LinkItONEDevGroup/LASS/IASS/IASS_BASIC/Docs/IASS完整安裝說明.pdf

1

# 開源的 IASS 室內環控系統

## Every One Can DIY Your Own Sensor Device

### IASS 是一套免費開源的室內環控系統，最早由凌陽創新科技開發並免費釋出。透過

### Arduino 開發板，搭配市面上常見且價廉物美的感測器，不需要撰寫任何程式，希望讓任

### 何人皆能在 30 分鐘內行 DIY 組裝完成符合自己需求的感測裝置。

### IASS 開源程式碼下載：https://github.com/LinkItONEDevGroup/LASS/tree/master/IASS

### IASS 目前為 LASS 的一個子計劃，也歡迎開發者們加入 IASS 予以修改精進，並持續增

### 加新的功能，如果您有興趣，請加入 LASS 的 FB 社團：

### https://www.facebook.com/groups/1607718702812067/

2

3

4

### A) IASS 特色

### 任何人皆能 DIY 感測裝置：

不需要程式設計或相關電子工程知識，每個人皆能 DIY 自己的環控系統。

### 支援多種感測功能：

目前支援 12 種環境感應功能：溫度,溼度,漏水,噪音,一氧化碳,天然氣, PM2.5, PM10, PM100, 二氧

化碳,環境光照度，可依自身需求決定要加裝的感應器。

### 不需要撰寫程式：

提供現成的 Arduino 程式可直接使用，分為 sensor 與 device 兩種，使用者可依需求選擇不同的

sensors 程式搭配成 device。

### 提供預設搭配好的感測裝置：

除了使用者可自行搭配決定感測器種類外，亦提供預設數種 device 直接使用：

- Office 辦公室：溫溼、PM2.5、CO2、光照度
- 電腦機房：溫溼、漏水、可燃氣體
- 家居室內：溫溼、一氧化碳、天然氣

### 自動上傳 ThingSpeak：

您可以讓組裝後的 IASS device 將資料自動上傳 ThingSpeak 以提供遠端瀏覽觀看（需自行註冊

ThingSpeak 帳號並於程式中放入 API KEY）

### 支援上傳指定 server：

除上傳 ThingSpeak 之外，亦可選擇將資料傳送到指定的 server 來接收(使用 GET)，目前 IASS 也

有提供一 PHP 編寫的中控台網站。

### B) IASS 的安裝步驟

5

A.1) 選擇您需要的感測裝置類型，購買零件材料開始 IY。

IASS 目前提供下列三種組裝範例。

- 辦公室專用
- 居家安全專用
- 機房專用

您也可以從 IASS GitHub 的 Sensors_support 目錄中選擇需要的感應器程式來組裝自己的感應裝

置。

A.2) 決定您的裝置要將資料上傳 ThingSpeak 還是傳到特定的伺服器。

- 若要上傳 ThingSpeak，請選擇 _thingspeak 資料夾的 Arduino 程式。
- 若要傳到指定伺服器，請選擇 _selfserver 資料夾的 Arduino 程式。

A.3) 決定是否要加裝 LCD？

A.4) 開始燒錄 Arduino 程式。

A.5) 如果您選擇上傳 ThingSpeak，可開始進行 ThingSpeak 設定

如果您選擇傳到 IASS 的伺服器，請開始安裝設定主機環境。

### C) 辦公室專用感測裝置的安裝步驟

材料準備

本裝置範例支援溫溼、PM2.5、CO2 及光照度等四種感測器功能，所需要的材料如下：

1. | Arduino UNO 主板 | x 1

http://www.icshop.com.tw/product_info.php/products_id/20369

2. | W5100 R3 network shield | x 1

http://goods.ruten.com.tw/item/show?21434006463160

3. | DHT-22 sensor | x 1（溫溼度用）

http://www.icshop.com.tw/product_info.php/products_id/12478

4. | G3 PM2.5 感測器 | x 1（PM2.5 用）

http://www.icshop.com.tw/product_info.php/products_id/20460

6

5. | CO2 感測器 MH-Z16 | x 1（二氧化碳用）

http://www.icshop.com.tw/product_info.php/products_id/14133

6. | 光照度感測器 TEMT6000 | x 1（光照度使用）

http://www.icshop.com.tw/product_info.php/products_id/11432

7. | 9V 變壓器 | x 1

（如果您同時裝上很多感應器，建議使用 9V 變壓器取代 USB，以避免電源不足）

http://www.icshop.com.tw/product_info.php/products_id/17470

8. | 迷你麵包板 | x 1

http://www.icshop.com.tw/product_info.php/products_id/11516

9. | 杜邦線 | 數條

http://www.icshop.com.tw/product_info.php/products_id/12374

10. 小型Ｌ型立書夾 | x 1（$39 元店有很多）

準備好了？開始組裝吧！

溫溼度感測

A）首先，將材料#1 與材料#2 合體如下：

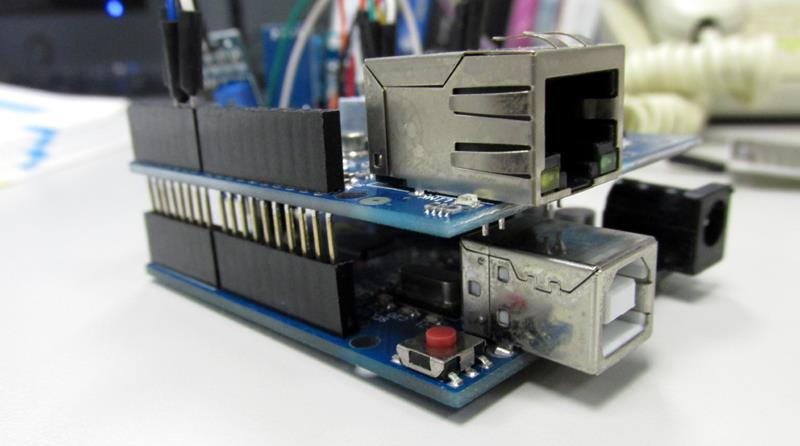
[picture p16: figure]

B）把材料#3 插上，注意一下左圖它的腳位

7

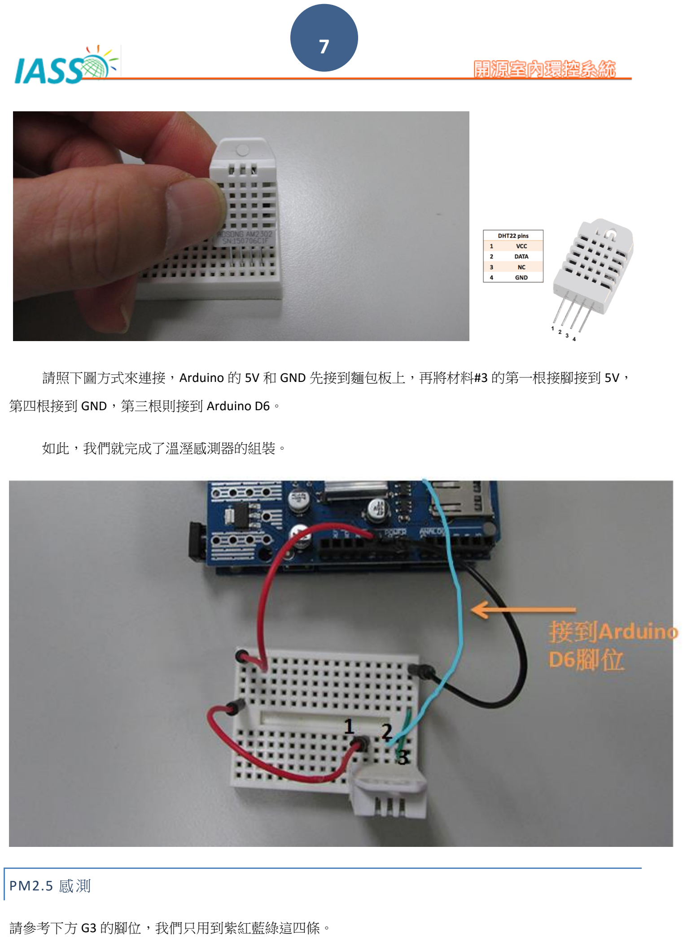
[picture p17: page 7]

請照下圖方式來連接，Arduino 的 5V 和 GND 先接到麵包板上，再將材料#3 的第一根接腳接到 5V，

第四根接到 GND，第三根則接到 Arduino D6。

如此，我們就完成了溫溼感測器的組裝。

PM2.5 感測

請參考下方 G3 的腳位，我們只用到紫紅藍綠這四條。

8

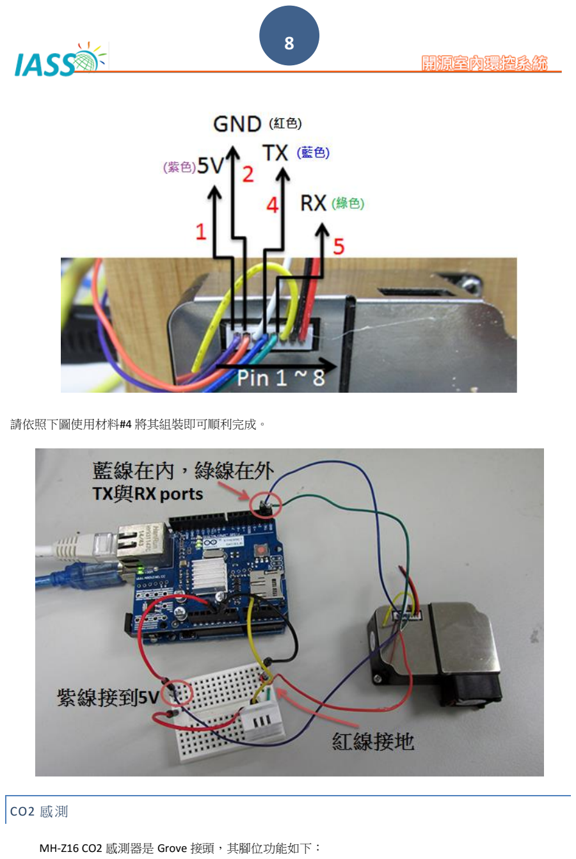
[picture p18: page 8]

請依照下圖使用材料#4 將其組裝即可順利完成。

CO2 感測

MH-Z16 CO2 感測器是 Grove 接頭，其腳位功能如下：

9

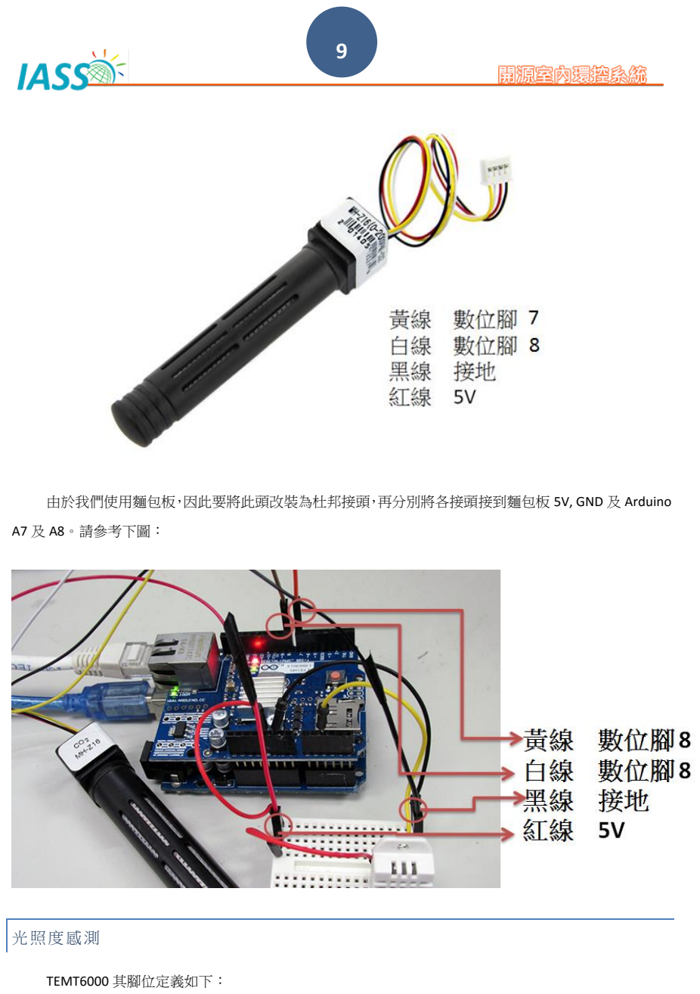
[picture p19: page 9]

由於我們使用麵包板，因此要將此頭改裝為杜邦接頭，再分別將各接頭接到麵包板 5V, GND 及 Arduino

A7 及 A8。請參考下圖：

光照度感測

TEMT6000 其腳位定義如下：

10

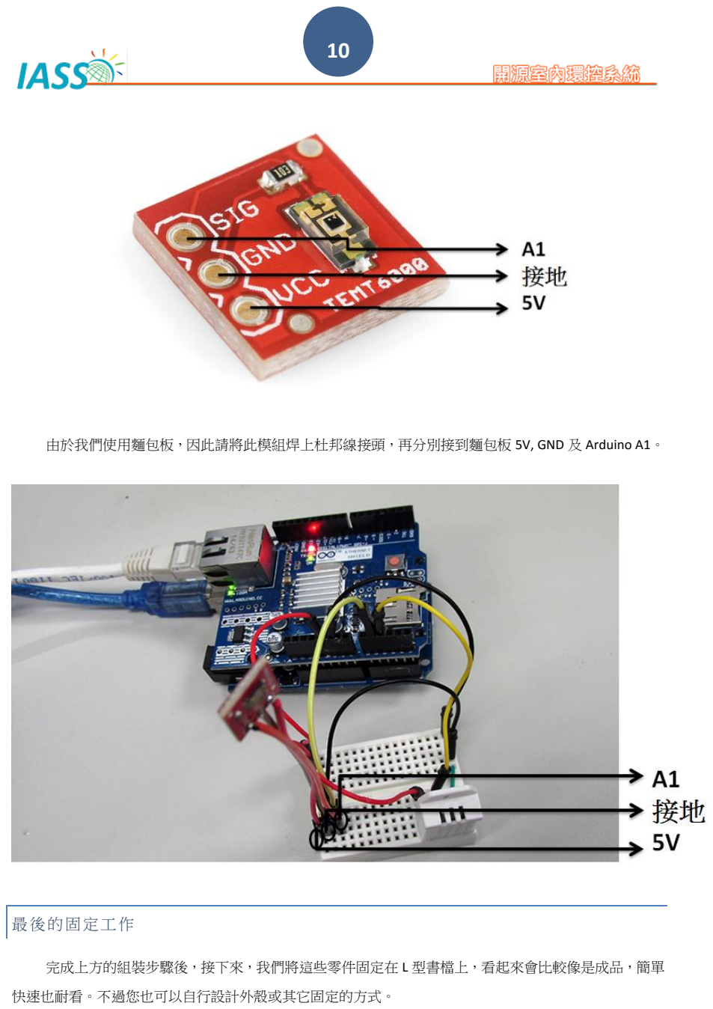
[picture p20: page 10]

由於我們使用麵包板，因此請將此模組焊上杜邦線接頭，再分別接到麵包板 5V, GND 及 Arduino A1。

最後的固定工作

完成上方的組裝步驟後，接下來，我們將這些零件固定在 L 型書檔上，看起來會比較像是成品，簡單

快速也耐看。不過您也可以自行設計外殼或其它固定的方式。

11

L 型書檔如果您使用的是木板材質，那麼可以直接用螺絲釘將所材料零件鎖上固定，如果使用的是鐵

或塑膠材質，那麼可能需要使用熱熔膠來固定。

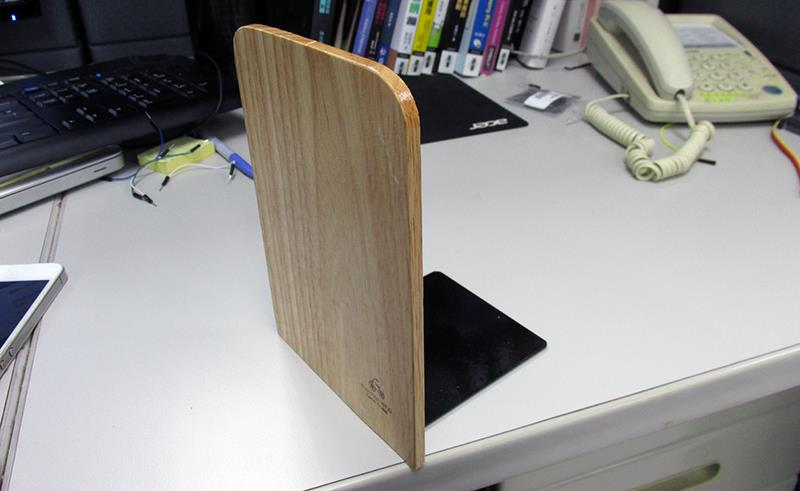
[picture p21: figure]

先將各零件要擺放位置先來預排看看。由於我們做的是一台可偵測溫溼度、PM2.5、二氧化碳、環境

光照度的感測裝置，因此有總共四個零件（Arduino 主板+W5100、迷你麵包板、G3 PM2.5 感測器、CO2 感

測器），把所有零件依照上述方式組裝好之後，預定擺放位置如下：

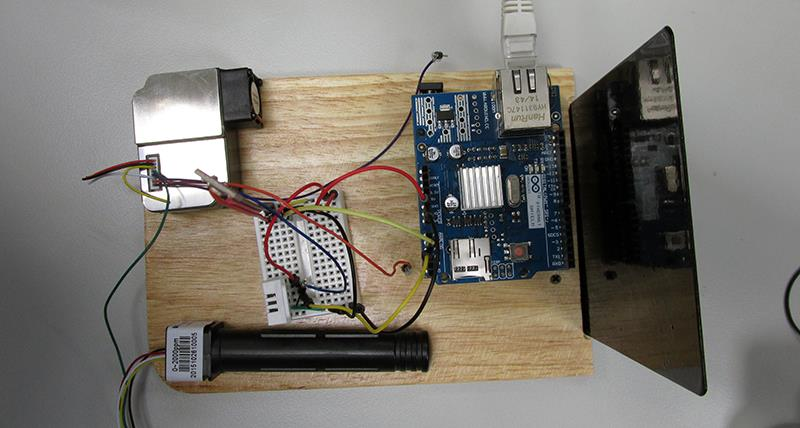
[picture p22: figure]

確定好位置之後就可以用螺絲將它們固定起來。好了，不用半小時，我們很快就能完成一台可偵測多

種環境狀態的感測裝置。

12

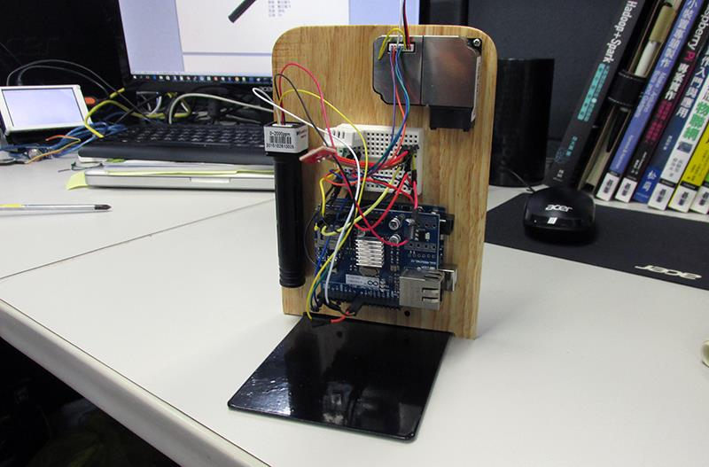
[picture p23: figure]

完成了！

### D) 居家專用感測裝置的安裝步驟

材料準備

1. | Arduino UNO 主板 | x 1

http://www.icshop.com.tw/product_info.php/products_id/20369

2. | W5100 R3 network shield | x 1

http://goods.ruten.com.tw/item/show?21434006463160

3. | DHT-22 sensor | x 1（溫溼度用）

http://www.icshop.com.tw/product_info.php/products_id/12478

4. | MQ7 感測器 | x 1（偵測一氧化碳）

http://www.icshop.com.tw/product_info.php/products_id/12491

5. | MQ4 感測器 | x 1（偵測瓦斯天然氣）

http://www.icshop.com.tw/product_info.php/products_id/12488

13

6. | 9V 變壓器 | x 1

（如果您同時裝上很多感應器，建議使用 9V 變壓器取代 USB，以避免電源不足）

http://www.icshop.com.tw/product_info.php/products_id/17470

7. | 迷你麵包板 | x 1

http://www.icshop.com.tw/product_info.php/products_id/11516

8. | 杜邦線 | 數條

http://www.icshop.com.tw/product_info.php/products_id/12374

9. | 小型Ｌ型立書夾 | x 1（$39 元店有很多）

準備好了？開始組裝吧！

溫溼度感測

A）首先，將材料#1 與材料#2 合體如下：

B）把材料#3 插上，注意一下左圖它的腳位

14

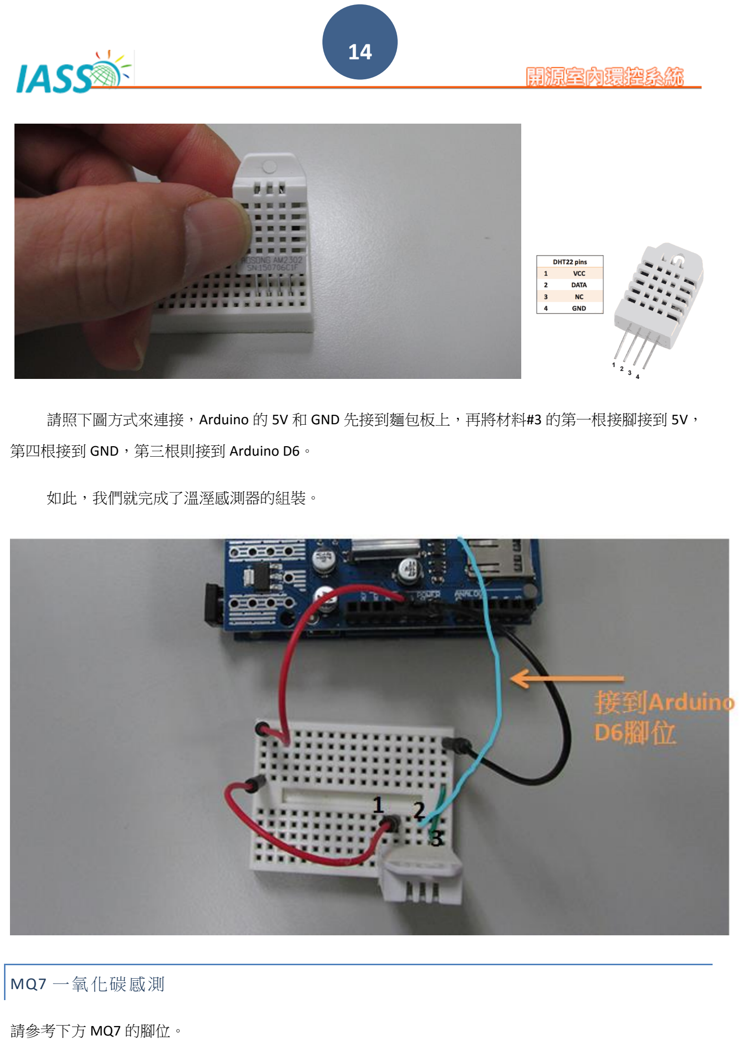
[picture p24: page 14]

請照下圖方式來連接，Arduino 的 5V 和 GND 先接到麵包板上，再將材料#3 的第一根接腳接到 5V，

第四根接到 GND，第三根則接到 Arduino D6。

如此，我們就完成了溫溼感測器的組裝。

MQ7 一氧化碳感測

請參考下方 MQ7 的腳位。

15

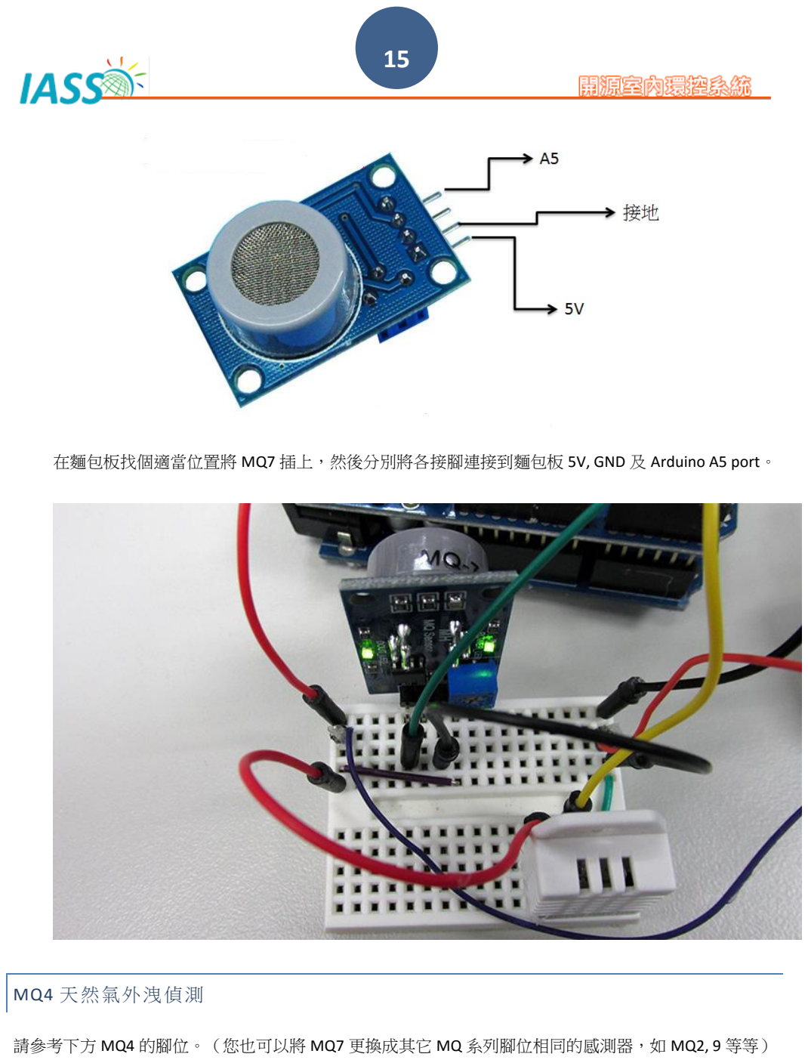
[picture p25: page 15]

在麵包板找個適當位置將 MQ7 插上，然後分別將各接腳連接到麵包板 5V, GND 及 Arduino A5 port。

MQ4 天然氣外洩偵測

請參考下方 MQ4 的腳位。（您也可以將 MQ7 更換成其它 MQ 系列腳位相同的感測器，如 MQ2, 9 等等）

16

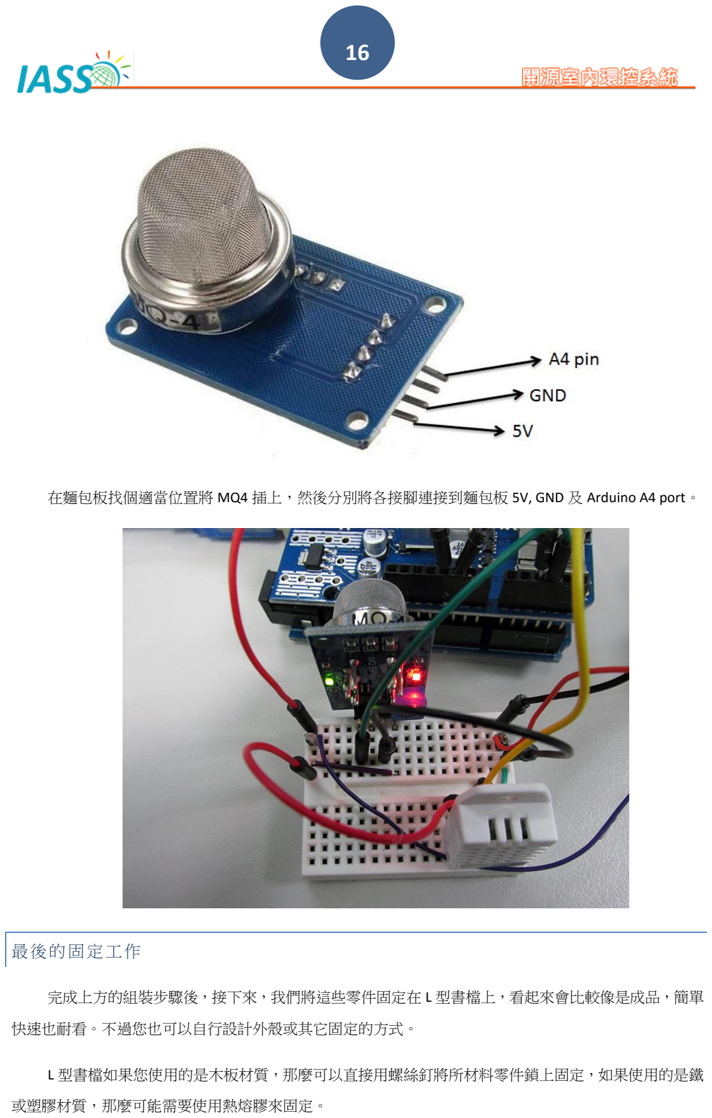
[picture p26: page 16]

在麵包板找個適當位置將 MQ4 插上，然後分別將各接腳連接到麵包板 5V, GND 及 Arduino A4 port。

最後的固定工作

完成上方的組裝步驟後，接下來，我們將這些零件固定在 L 型書檔上，看起來會比較像是成品，簡單

快速也耐看。不過您也可以自行設計外殼或其它固定的方式。

L 型書檔如果您使用的是木板材質，那麼可以直接用螺絲釘將所材料零件鎖上固定，如果使用的是鐵

或塑膠材質，那麼可能需要使用熱熔膠來固定。

17

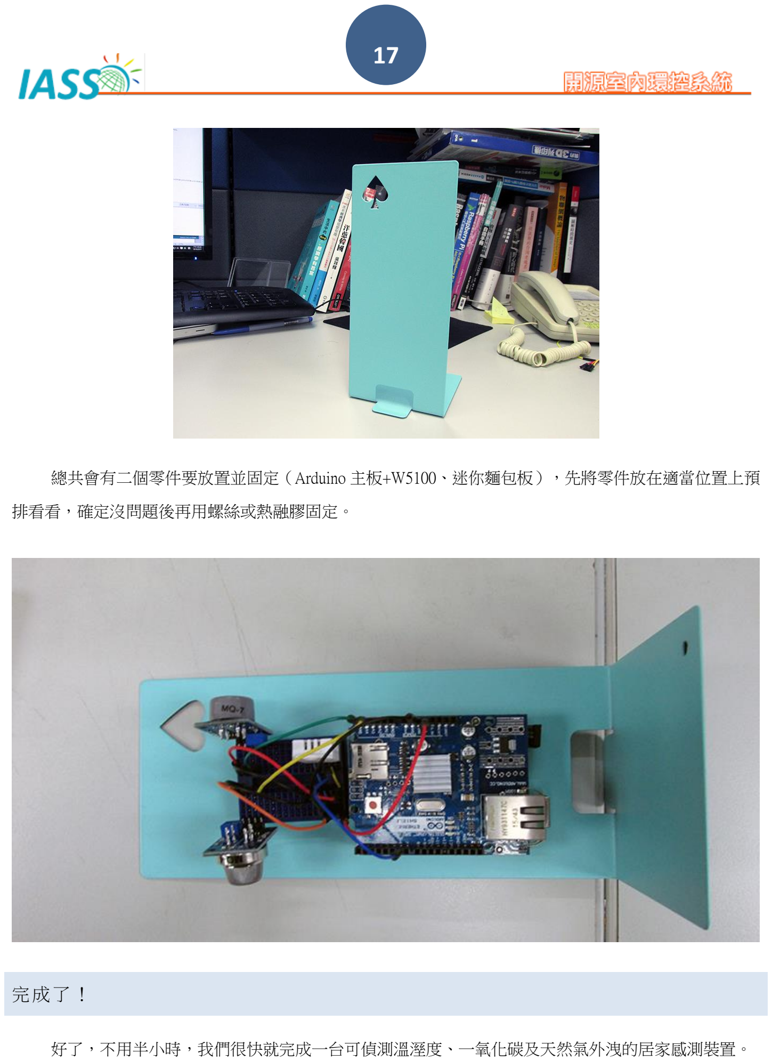
[picture p27: page 17]

總共會有二個零件要放置並固定（Arduino 主板+W5100、迷你麵包板），先將零件放在適當位置上預

排看看，確定沒問題後再用螺絲或熱融膠固定。

完成了！

好了，不用半小時，我們很快就完成一台可偵測溫溼度、一氧化碳及天然氣外洩的居家感測裝置。

18

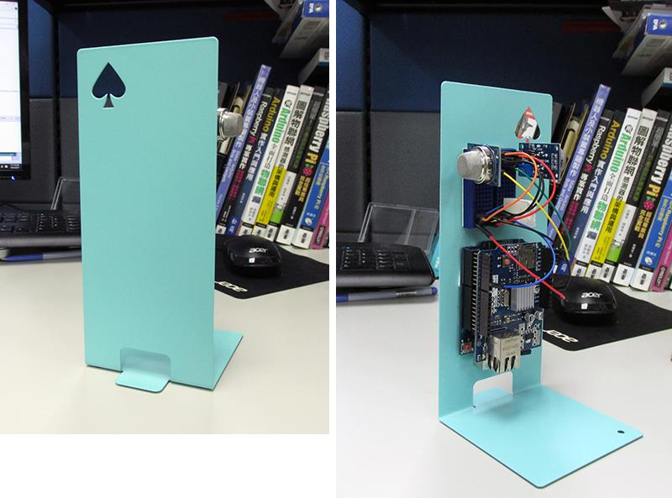
[picture p28: figure]

### E) 居家專用感測裝置的安裝步驟

材料準備

1. | Arduino UNO 主板 | x 1

http://www.icshop.com.tw/product_info.php/products_id/20369

2. | W5100 R3 network shield | x 1

http://goods.ruten.com.tw/item/show?21434006463160

3. | DHT-22 sensor | x 1（溫溼度用）

http://www.icshop.com.tw/product_info.php/products_id/12478

4. | FC-37 雨水感測器： | x 1（偵測高架地板漏水）

http://www.icshop.com.tw/product_info.php/products_id/12483

5. | MQ2 感測器 | x 1（偵測易燃氣體及煙霧）

http://www.icshop.com.tw/product_info.php/products_id/14133

19

6. | 9V 變壓器 | x 1

（如果您同時裝上很多感應器，建議使用 9V 變壓器取代 USB，以避免電源不足）

http://www.icshop.com.tw/product_info.php/products_id/17470

7. | 迷你麵包板 | x 1

http://www.icshop.com.tw/product_info.php/products_id/11516

8. | 杜邦線 | 數條

http://www.icshop.com.tw/product_info.php/products_id/12374

9. | 小型Ｌ型立書夾 | x 1（$39 元店有很多）

準備好了？開始組裝吧！

溫溼度感測

A）首先，將材料#1 與材料#2 合體如下：

B）把材料#3 插上，注意一下左圖它的腳位

20

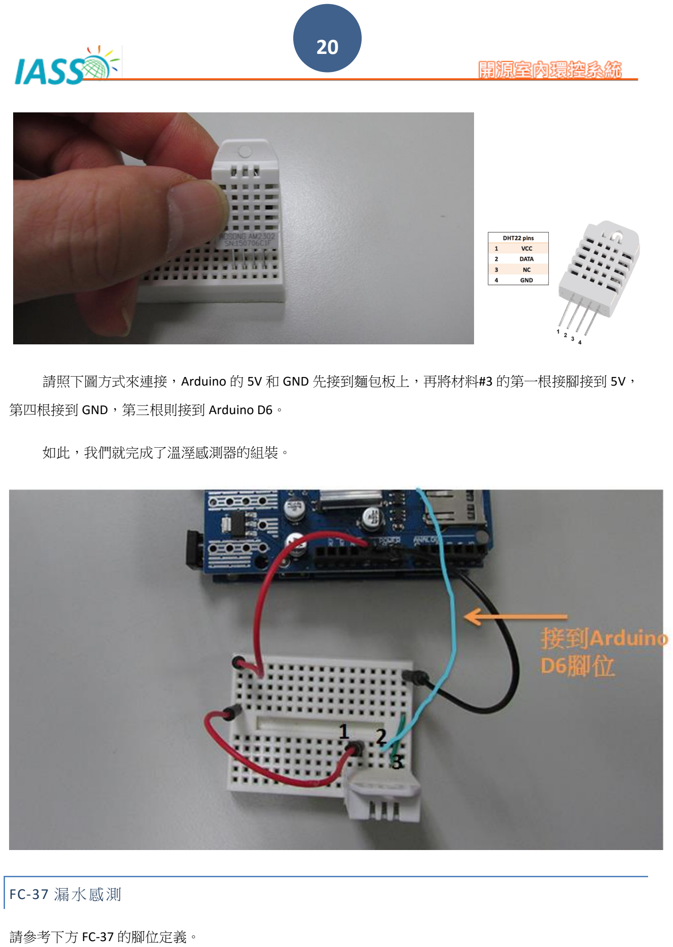
[picture p29: page 20]

請照下圖方式來連接，Arduino 的 5V 和 GND 先接到麵包板上，再將材料#3 的第一根接腳接到 5V，

第四根接到 GND，第三根則接到 Arduino D6。

如此，我們就完成了溫溼感測器的組裝。

FC-37 漏水感測

請參考下方 FC-37 的腳位定義。

21

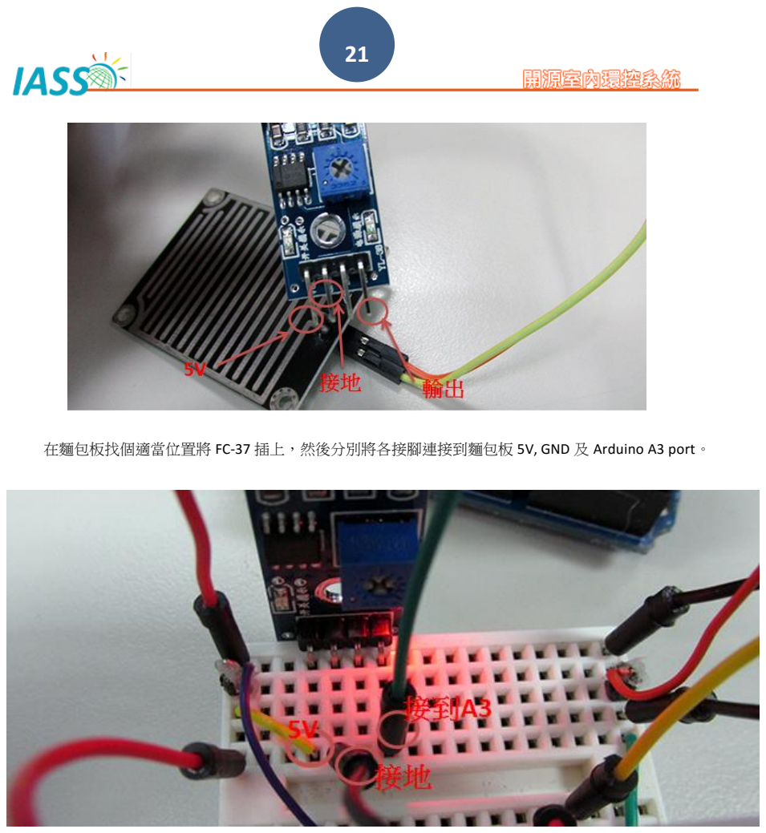
[picture p30: page 21]

在麵包板找個適當位置將 FC-37 插上，然後分別將各接腳連接到麵包板 5V, GND 及 Arduino A3 port。

22

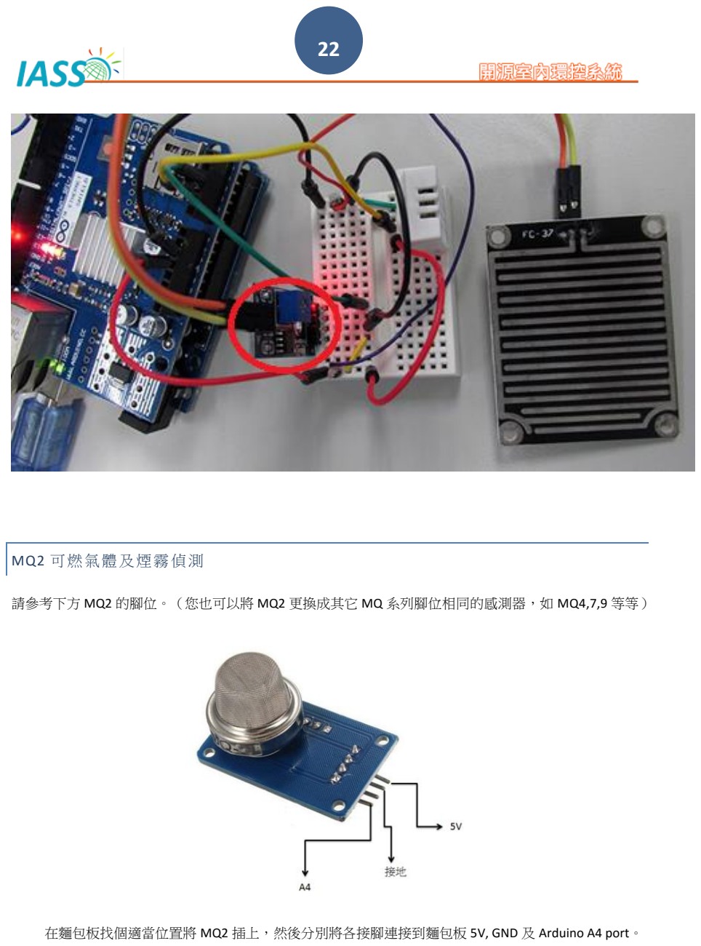
[picture p31: page 22]

MQ2 可燃氣體及煙霧偵測

請參考下方 MQ2 的腳位。（您也可以將 MQ2 更換成其它 MQ 系列腳位相同的感測器，如 MQ4,7,9 等等）

在麵包板找個適當位置將 MQ2 插上，然後分別將各接腳連接到麵包板 5V, GND 及 Arduino A4 port。

23

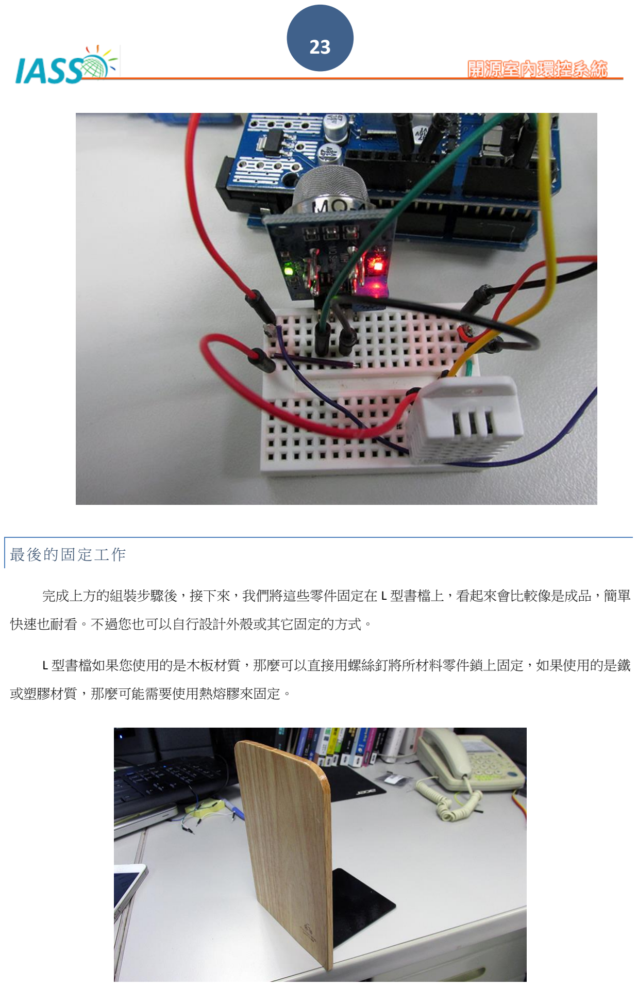
[picture p32: page 23]

最後的固定工作

完成上方的組裝步驟後，接下來，我們將這些零件固定在 L 型書檔上，看起來會比較像是成品，簡單

快速也耐看。不過您也可以自行設計外殼或其它固定的方式。

L 型書檔如果您使用的是木板材質，那麼可以直接用螺絲釘將所材料零件鎖上固定，如果使用的是鐵

或塑膠材質，那麼可能需要使用熱熔膠來固定。

24

總共會有三個零件要放置並固定（Arduino 主板+W5100、迷你麵包板、FC-37 的外接雨水感測板），

先將零件放在適當位置上預排看看，確定沒問題後再用螺絲或熱融膠固定。

完成了！

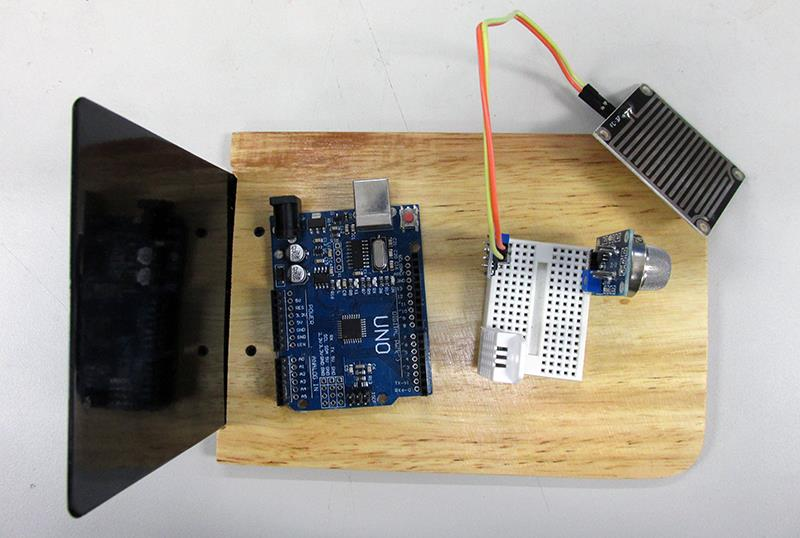
[picture p33: figure]

好了，不用半小時，我們很快就能完成一台可偵測溫溼度、漏水及火災的機房感測裝置。

25

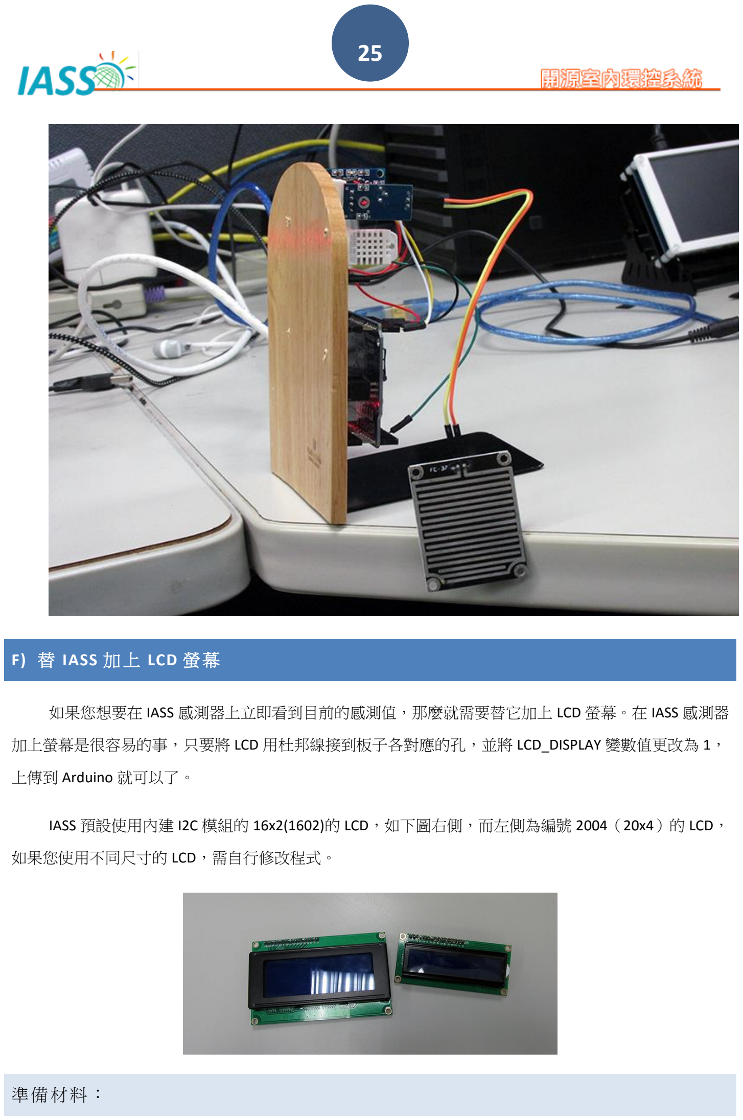
[picture p34: page 25]

F) 替 IASS 加上 LCD 螢幕

如果您想要在 IASS 感測器上立即看到目前的感測值，那麼就需要替它加上 LCD 螢幕。在 IASS 感測器

加上螢幕是很容易的事，只要將 LCD 用杜邦線接到板子各對應的孔，並將 LCD_DISPLAY 變數值更改為 1，

上傳到 Arduino 就可以了。

IASS 預設使用內建 I2C 模組的 16x2(1602)的 LCD，如下圖右側，而左側為編號 2004（20x4）的 LCD，

如果您使用不同尺寸的 LCD，需自行修改程式。

準備材料：

26

1. LCD 1602 5V LCM IIC I2C 16x2 | $95 x 1

http://goods.ruten.com.tw/item/show?21408019307836

2. 杜邦線（母→公） | 數條

開始組裝吧！

接上 LCD

此類的 I2C LCD 模組皆有四個接腳如下：

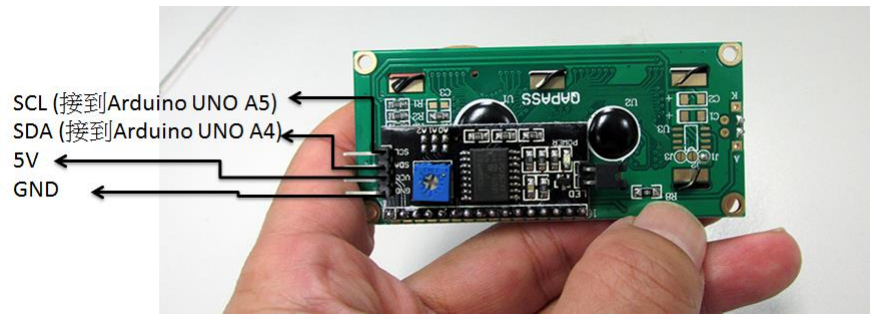
[picture p35: figure]

請參考下圖使用杜邦線將各接腳接到麵包板及 Arduino 上。

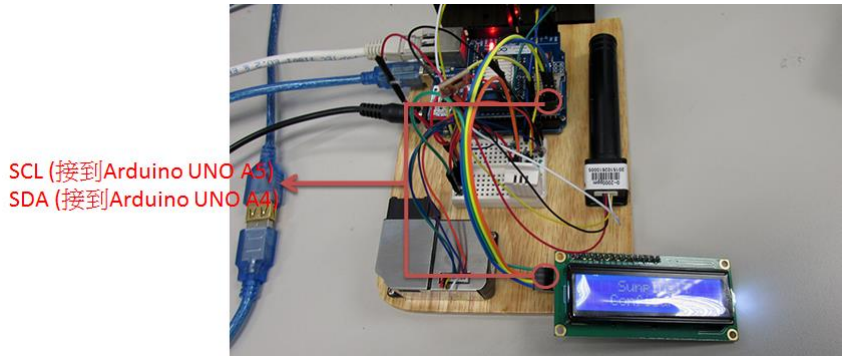
[picture p36: figure]

將 LCD 固定好

27

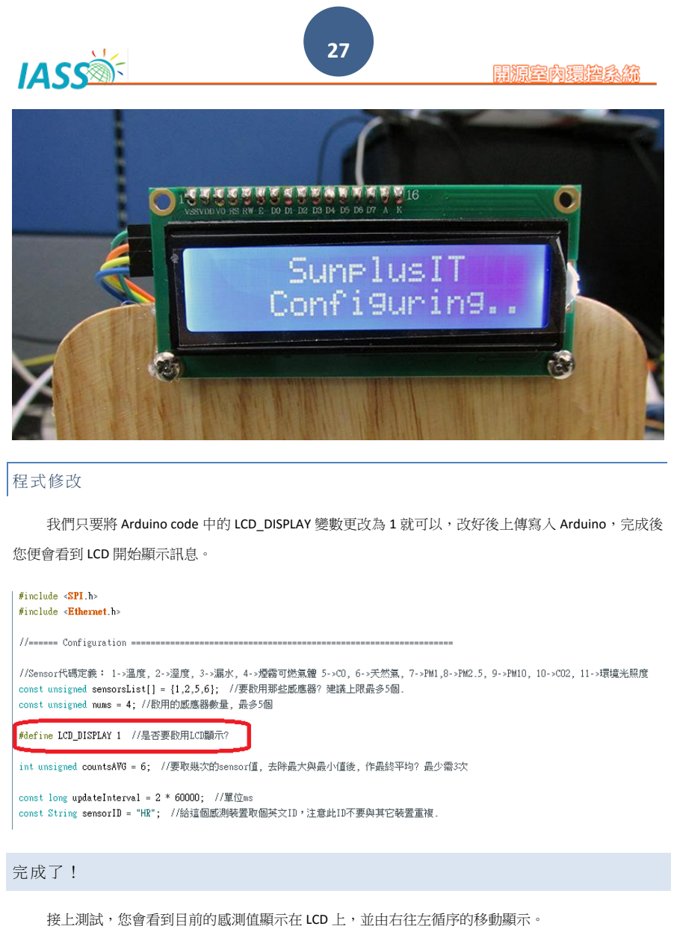
[picture p37: page 27]

程式修改

我們只要將 Arduino code 中的 LCD_DISPLAY 變數更改為 1 就可以，改好後上傳寫入 Arduino，完成後

您便會看到 LCD 開始顯示訊息。

完成了！

接上測試，您會看到目前的感測值顯示在 LCD 上，並由右往左循序的移動顯示。

28

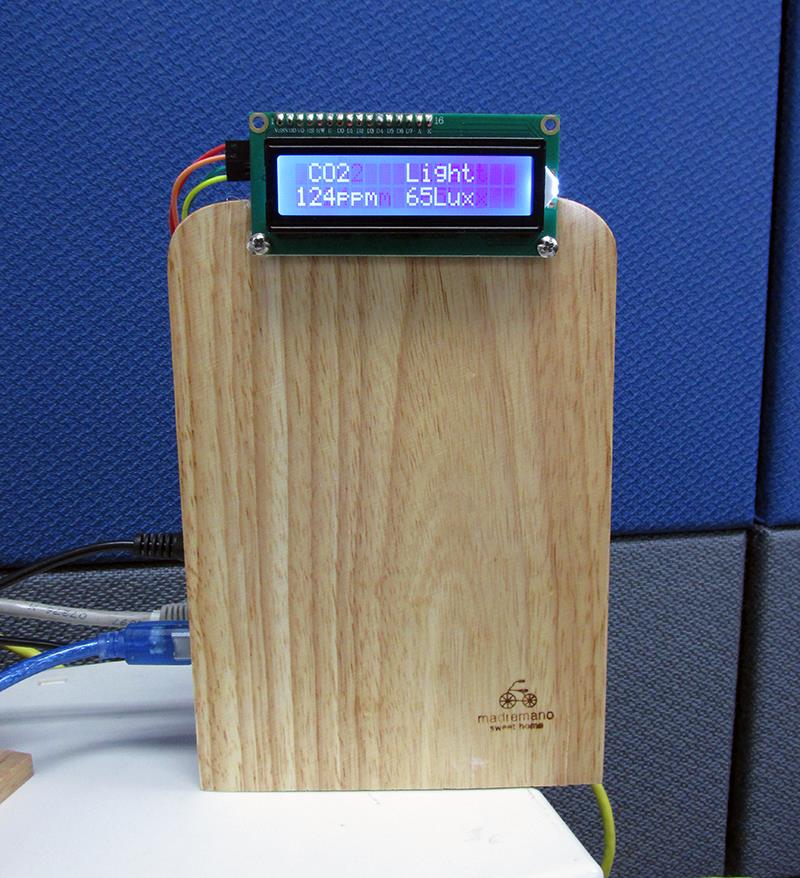
[picture p38: figure]

G) 申請及設定 THINKSPEAK

要馬上看到感測裝置所搜集的資訊，以及各時段的記錄和變化曲線，除了自己架一台 server 來處理

之外，最快也最方便的方式就是使用 IoT 平台了，有些 IoT 平台是免費的，而且可以替你繪出詳細的統計

曲線，例如 FreeBoard、ThingSpeak 等等。

目前 IASS 系統支援 ThingSpeak，在您註冊 ThingSpeak 帳號之後，便可將專屬的 API KEY 放在 Arduino

程式中，系統便會搜集到的資料直接上傳 ThingSpeak 繪製如下圖：

註冊帳號並登入之後，請先在 My Channels 當中建立一個新 Channel，這個 Channel 您可以將它視為

剛剛所組裝好的感測設備資料接收顯示端。

29

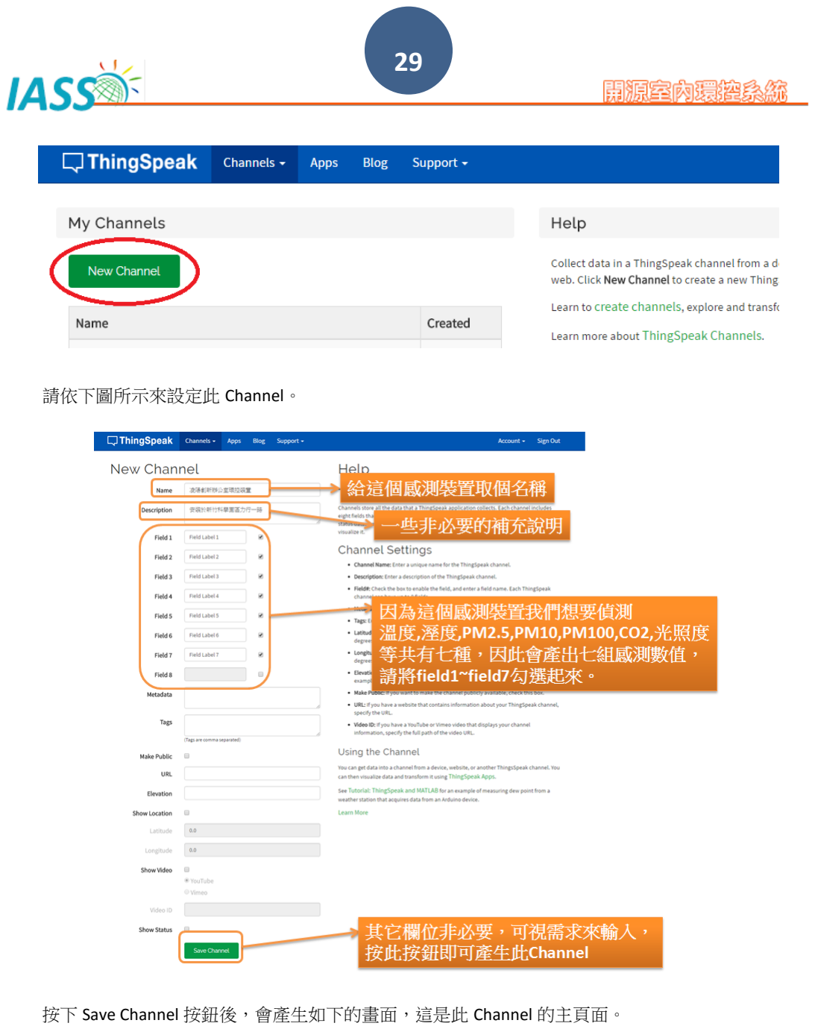
[picture p39: page 29]

請依下圖所示來設定此 Channel。

按下 Save Channel 按鈕後，會產生如下的畫面，這是此 Channel 的主頁面。

30

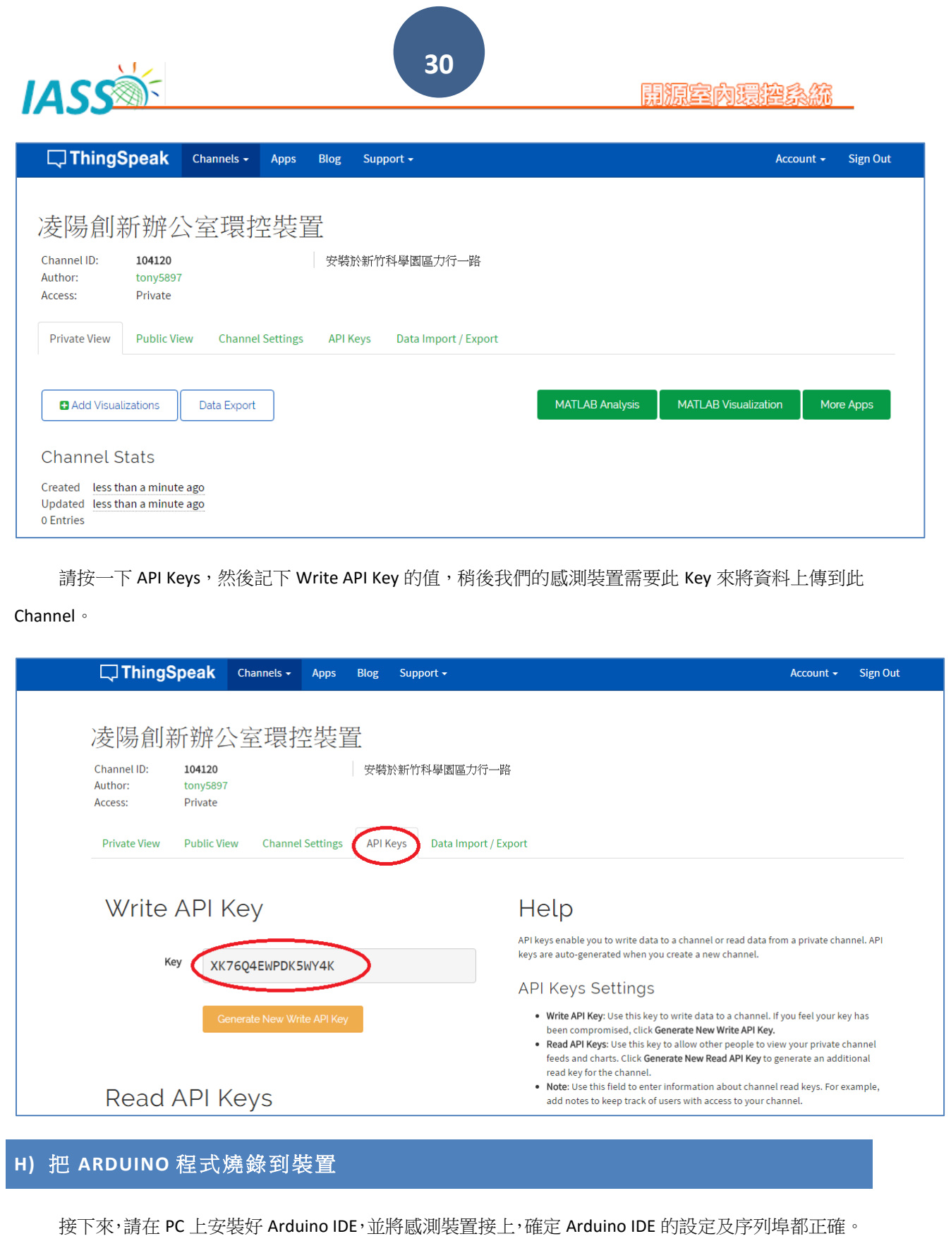
[picture p40: page 30]

請按一下 API Keys，然後記下 Write API Key 的值，稍後我們的感測裝置需要此 Key 來將資料上傳到此

Channel。

H) 把 ARDUINO 程式燒錄到裝置

接下來，請在 PC 上安裝好 Arduino IDE，並將感測裝置接上，確定 Arduino IDE 的設定及序列埠都正確。

31

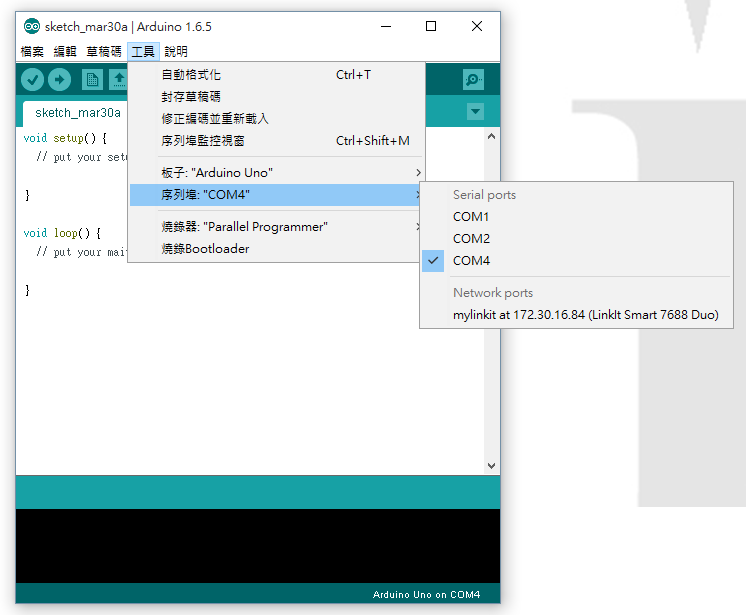
[picture p41: figure]

到 https://github.com/LinkItONEDevGroup/LASS/tree/master/IASS/IAAS_CODES/devices 目錄下，進入

Office 目錄，將 office.ino 程式內容 Copy 下來 Paste 到 Arduino IDE，請視需要修改下方的參數（紅色部份是

必要的修改）：

//Sensor 代碼定義： 1->溫度, 2->溼度, 3->漏水, 5->CO, 6->天然氣, 7->PM2.5,8->PM10, 9->PM100, 10->CO2, , 11->環境光照度
const unsigned sensorsList[] = {1,2,7,8,9,10,11}; | //要啟用那些感應器?
const unsigned nums = 7; | //啟用的感應器數量

const String sensorID = "MR"; //給這個感測裝置取個英文 ID，注意此 ID 不要與其它裝置重複. const String deviceName = "電腦機房"; //說明此感測裝置用途或地點.
int unsigned countsAVG = 6; //要取幾次的 sensor 值, 去除最大與最小值後, 作最終平均? 最少需 3 次

const boolean uploadThingsSpeak = 1; //要上傳 ThingsSpeak? 是:1 , 否:0
const String writeAPIKey = "{你的 ThinkSpeak APIKEY}";
const long updateThingSpeakInterval = 5 * 60000; //單位 ms

const boolean uploadDataServer = 0; //要上傳指定的 server? 是:1 , 否:0
IPAddress DataServerIP(192,168,3,2); //將資料以 GET 方式傳到特定 server IP，若不需要上傳則用 "" const short DataServerPort = 80; //將資料以 GET 方式傳到特定 server 的 port 埠號
const String DataServerPage = "/iaas/update.php"; //將資料以 GET 方式傳到特定 server 的接收網頁路 徑

32

byte mac[] = { 0xDE, 0xAD, 0xBE, 0xEF, 0xFE, 0xED }; //請自行設定一組 MAC Address，可隨意指定，但 請勿跟網路上已有的網卡相同避免衝突
const boolean networkDHCP = 1; //使用 DHCP: 1, 使用固定 IP: 0

//---> 固定 IP,如果使用固定 IP 資訊請填入下方資訊
byte ip[] = { 10,0,0,35 }; | //如果沒有成功得到 DHCP 的位址, 則會使用這個 IP.
byte myDns[] = { 8,8,8,8 }; | //如果沒有成功得到來自 DHCP 的 DNS, 則會使用這個 DNS IP.
byte gateway[] = { 10,0,0,254 };
byte subnet[] = { 255, 255, 255, 0 };

修改後，便可直接燒錄至 Arduino（燒錄前請先把 G3 PM2.5 感測器的綠線不要插上，以避免 RX port

被佔用無法燒錄，燒錄成功後再插回）。

I) 設定 THINGSPEAK FIELD

在 Arduino 的序列埠監控視窗上，您會看到如下的訊息。

33

說明：

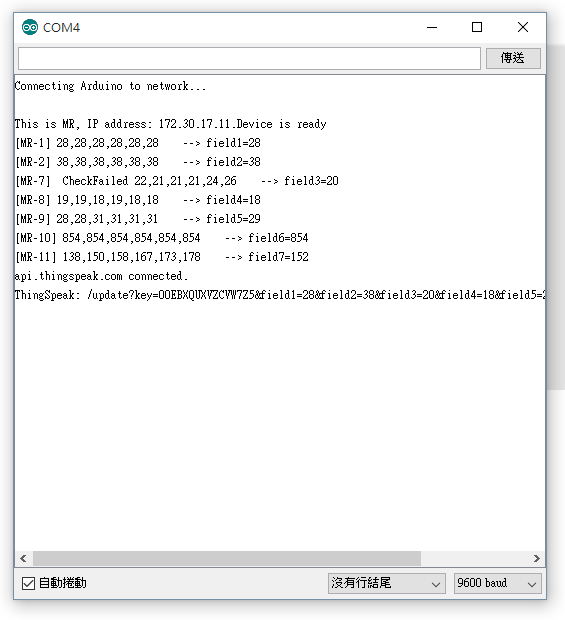
[picture p42: figure]

[MR-1] 28,28,28,28,28,28 | --> field1=28 | → 溫度會丟到 ThingSpeak 的 Field1
[MR-2] 38,38,38,38,38,38 | --> field2=38 | → 溼度會丟到 ThingSpeak 的 Field2
[MR-7] CheckFailed 22,21,21,21,24,26 | --> field3=20 → PM2.5 會丟到 ThingSpeak 的 Field3
[MR-8] 19,19,18,19,18,18 | --> field4=18 | → PM10 會丟到 ThingSpeak 的 Field4
[MR-9] 28,28,31,31,31,31 | --> field5=29 | → PM100 溼度會丟到 ThingSpeak 的 Field5
[MR-10] 854,854,854,854,854,854 | --> field6=854 | → CO2 會丟到 ThingSpeak 的 Field6
[MR-11] 138,150,158,167,173,178 | --> field7=152 | → 光照度會丟到 ThingSpeak 的 Field7

所以，我們可以準備回到 ThingSpeak 的 Channel 設定頁面，將各 Field 的內容補充進去。

34

再次進入 ThingSpeak，點選剛剛所建立的 Channel，您應該會發現各個 Field 都有各自獨立的統計圖，

且已經開始有資料進來了，您可以點選各 Field 圖示的修改按鈕，進行細部的修正，如 Title、Y 軸文字、上

下限等等。例如下圖：

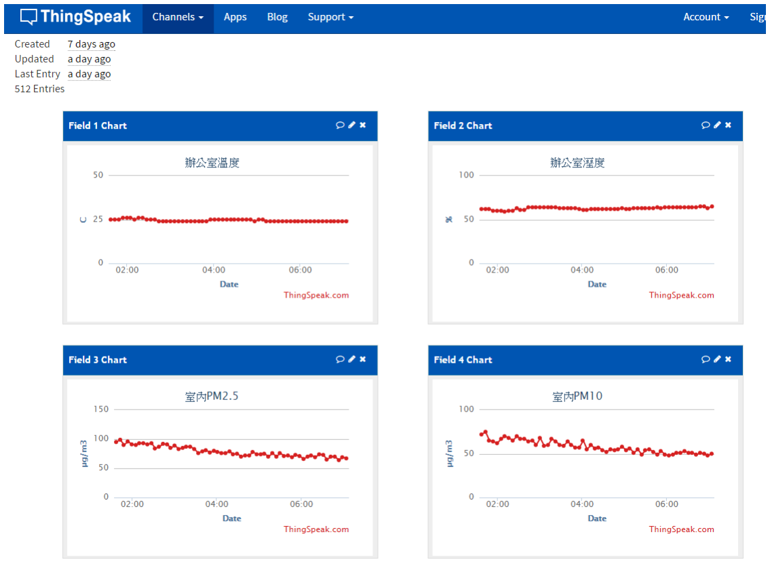
[picture p43: figure]

35

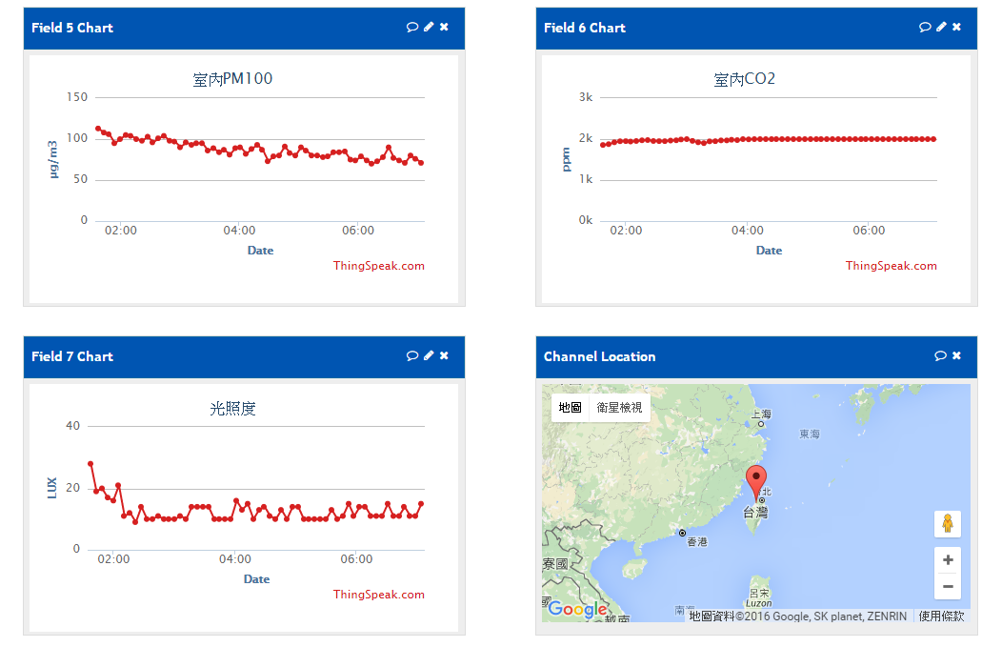
[picture p44: figure]

J) 自行架設 IASS 主機

IAAS 感測裝置除了可上傳資訊到 thingspeak.com 之外，也可傳送到到指定的 IP ，讓我們可將這些資

訊自行接收儲存下來，並自行開發程式來處理及運用這些資訊。IASS 本身也提供了一套基本的 IASS 主機程

式，提供使用者可快速的安裝使用。該範例為使用 PHP+mySQL 所編寫，安裝上相當容易，步驟如下：

A） 準備一個可執行 PHP + mySQL 的 web server，下載並解壓 IAASweb.zip。

B） 建立資料庫：下載 iaas_db.sql，並透過 phpMyAdmin 匯入 mySQL。

C） 透過 phpMyAdmin 新增一 mySQL account，將此帳號資訊填入 pdo.php。

D） 將各感應 device 的 ID 及 sensors 代號列表填入 pdo.php。

E） 將整個 IAASweb 目錄上傳 web server。

F） 將 web 主機相關資訊更新到各感應 device。

G） 後續修改及調整。

準備 WEB SERVER，

您可以使用一般的 PC，也可以用樹莓派 RPI 或香蕉派 BPI 搭配一台小型 LCD 螢幕來架設。

36

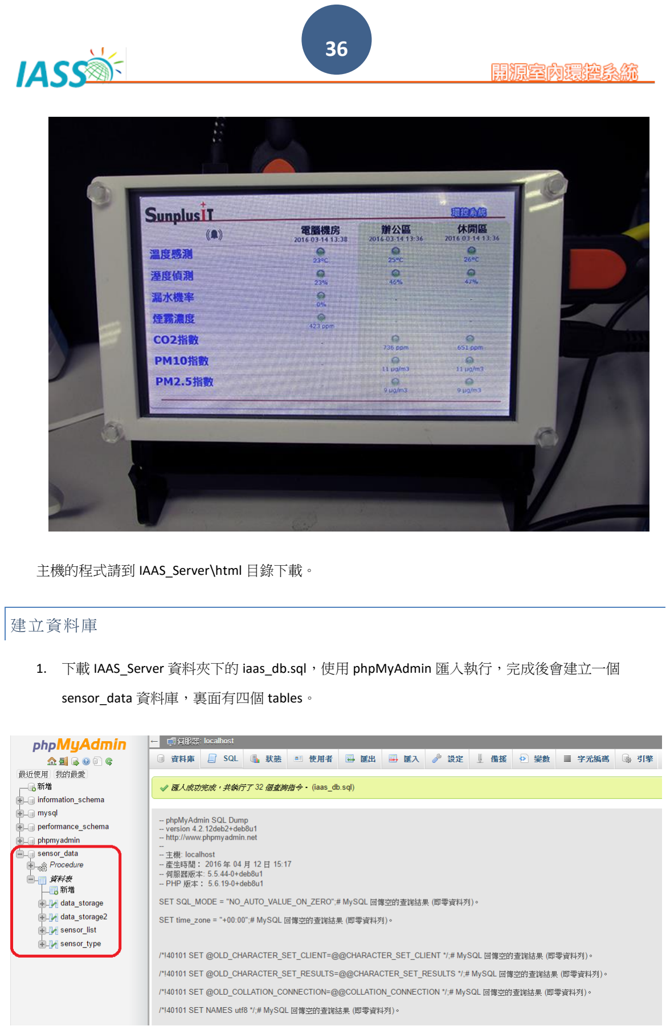
[picture p45: page 36]

主機的程式請到 IAAS_Server\html 目錄下載。

建立資料庫

1. 下載 IAAS_Server 資料夾下的 iaas_db.sql，使用 phpMyAdmin 匯入執行，完成後會建立一個

sensor_data 資料庫，裏面有四個 tables。

37

新增 MYSQL ACCOUNT

1. 透過 phpMyAdmin 新增一 mySQL 帳號，給予它存取 sensor_data 資料庫的權限。

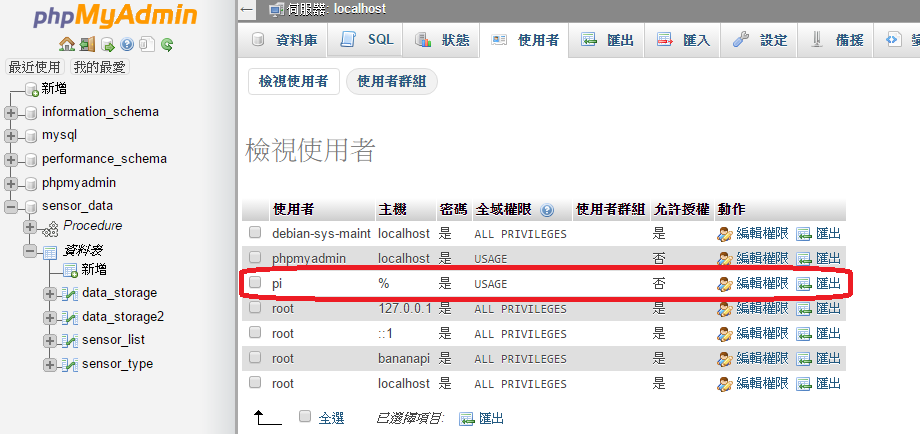
[picture p46: figure]

2. 編輯 conn/pdo.php 檔案，將剛剛新增的帳號及密碼填入。

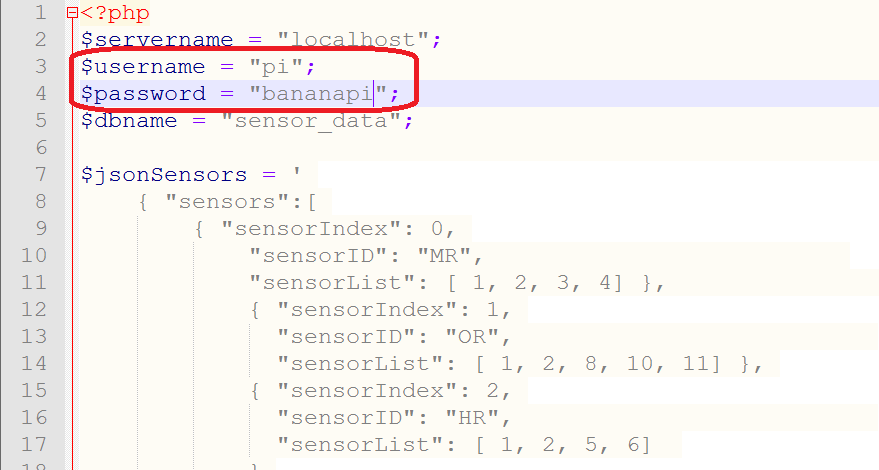
[picture p47: figure]

設定要顯示的裝置及 SENSORS

1. 接下來，我們要設定主機上要顯示那些感測器的資訊。請回頭檢視一下您目前使用中的 IAAS 感應

裝置，假設您目前有三台，請看一下它們的 Arduino Code，分別記下 sensorsList[]以及 sensorID 的

值。（這兩個值是可自行設定的）

第一台：

38

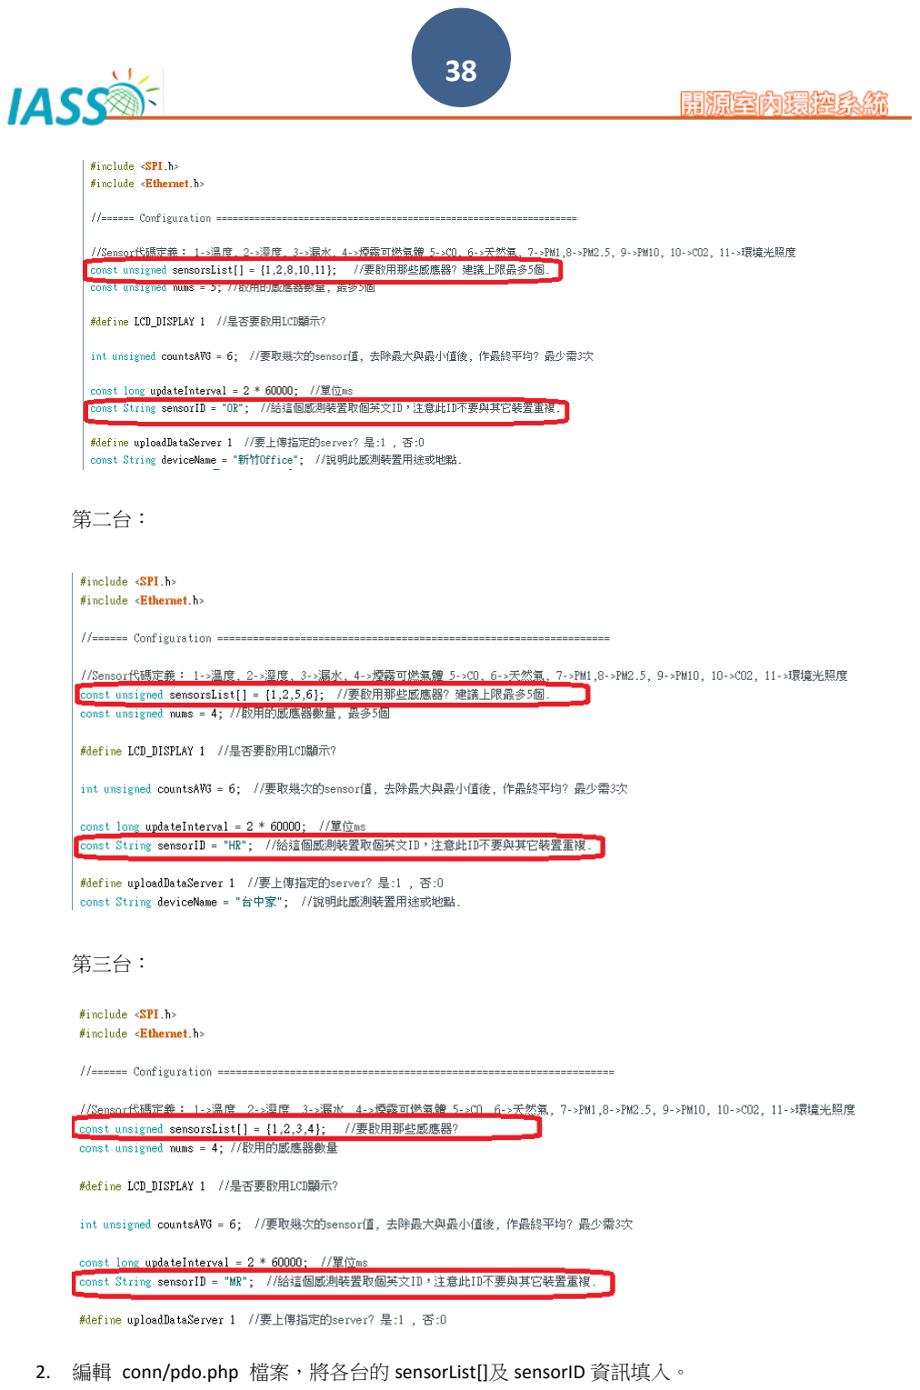
[picture p48: page 38]

第二台：

第三台：

2. 編輯 conn/pdo.php 檔案，將各台的 sensorList[]及 sensorID 資訊填入。

39

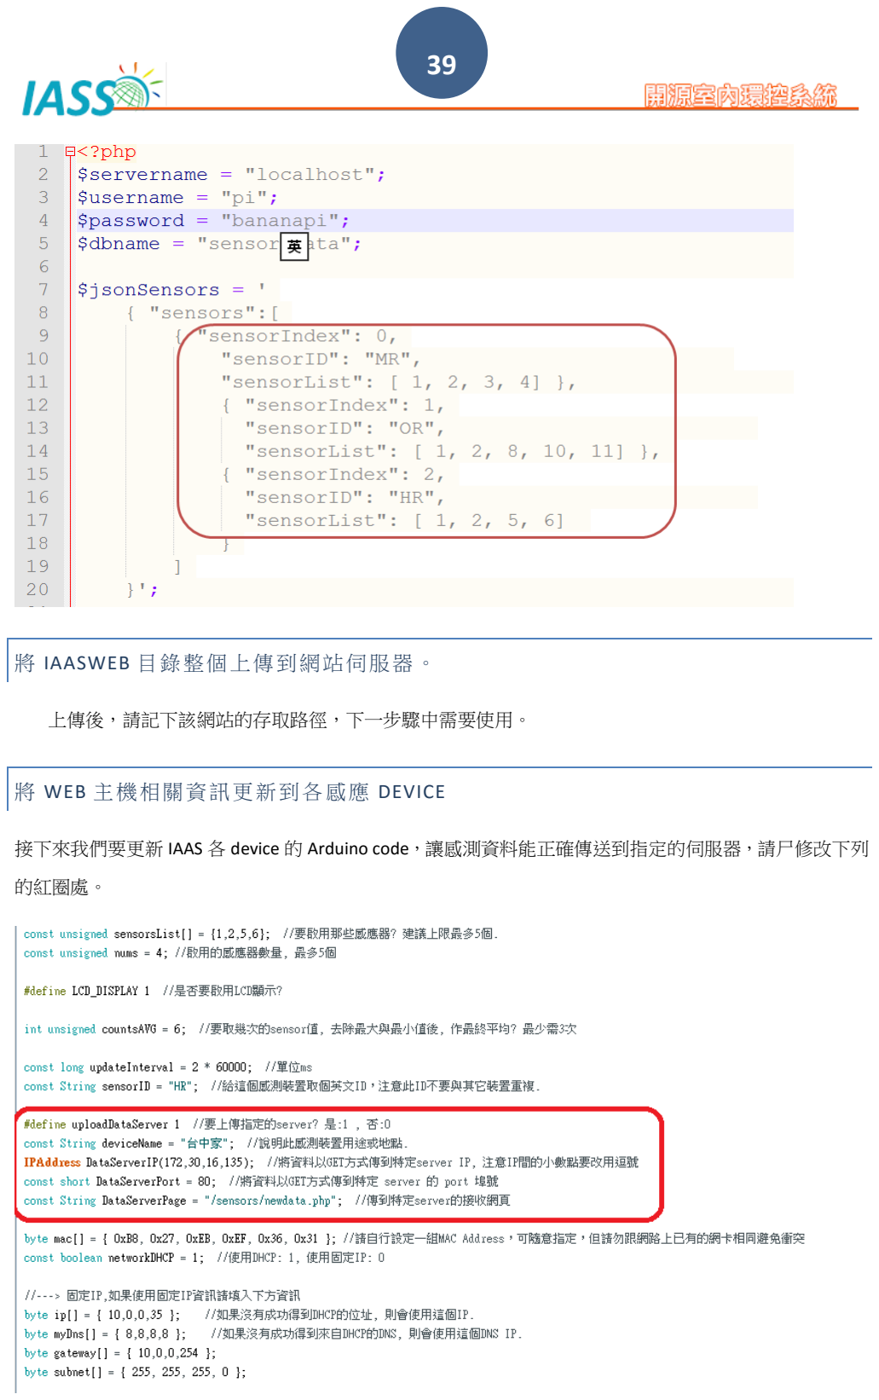
[picture p49: page 39]

將 IAASWEB 目錄整個上傳到網站伺服器。

上傳後，請記下該網站的存取路徑，下一步驟中需要使用。

將 WEB 主機相關資訊更新到各感應 DEVICE

接下來我們要更新 IAAS 各 device 的 Arduino code，讓感測資料能正確傳送到指定的伺服器，請尸修改下列

的紅圈處。

40

後續修改及調整

當網站開始有資料進來之後，進入網頁後您會發現所有燈號是紅色的，這是因為還未設定上限警示值

的緣故。

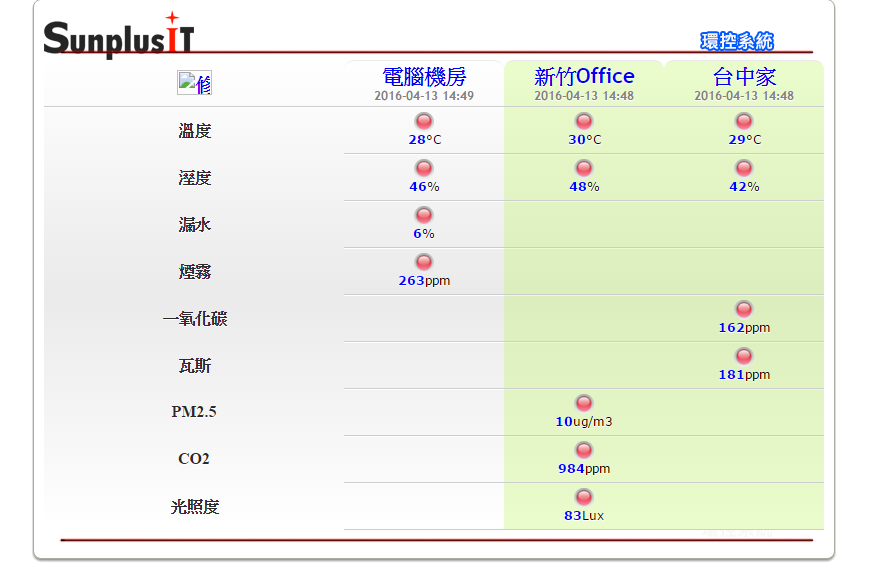
[picture p50: figure]

請進入 phpMyAdmin，修改 sensor_list 表格中 alarm_max 及 alarm_min 此兩項資訊，即可讓頁面正確

的顯示綠燈或紅燈。

41

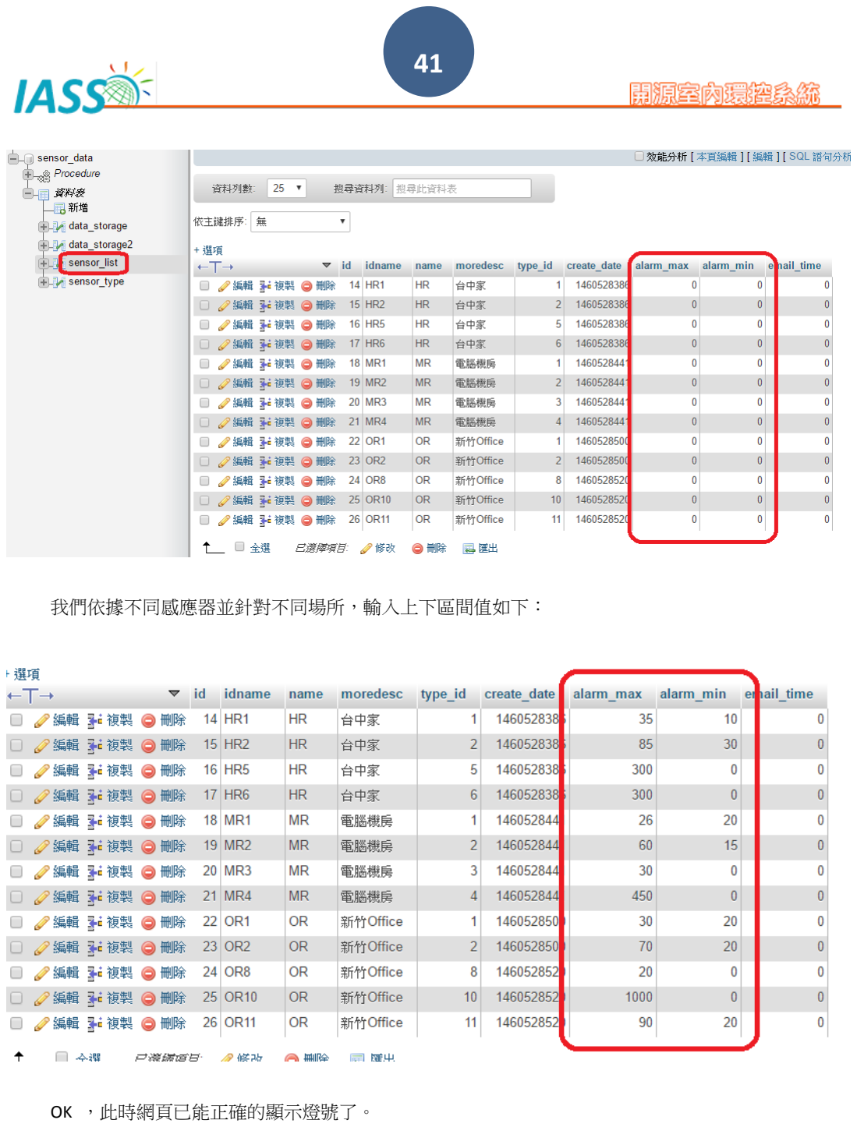
[picture p51: page 41]

我們依據不同感應器並針對不同場所，輸入上下區間值如下：

OK ，此時網頁已能正確的顯示燈號了。

42

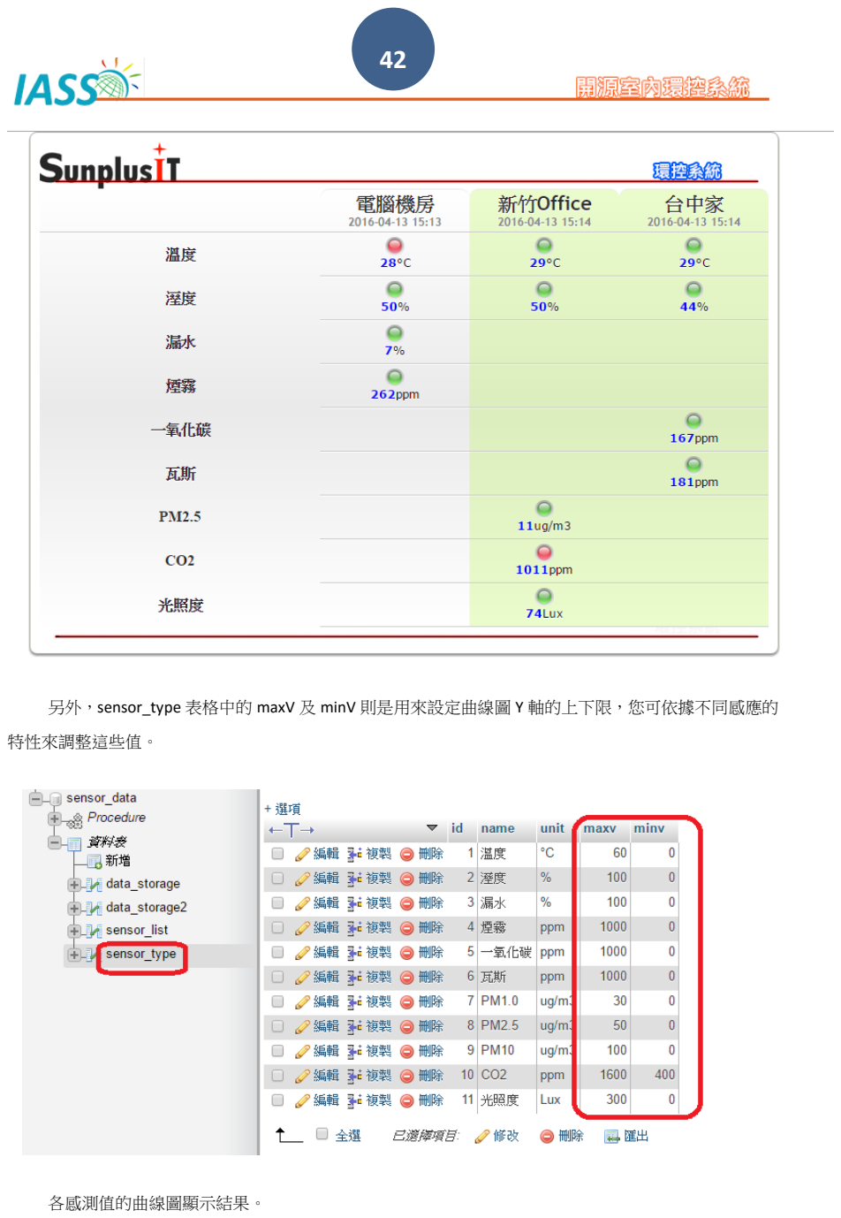
[picture p52: page 42]

另外，sensor_type 表格中的 maxV 及 minV 則是用來設定曲線圖 Y 軸的上下限，您可依據不同感應的

特性來調整這些值。

各感測值的曲線圖顯示結果。

43

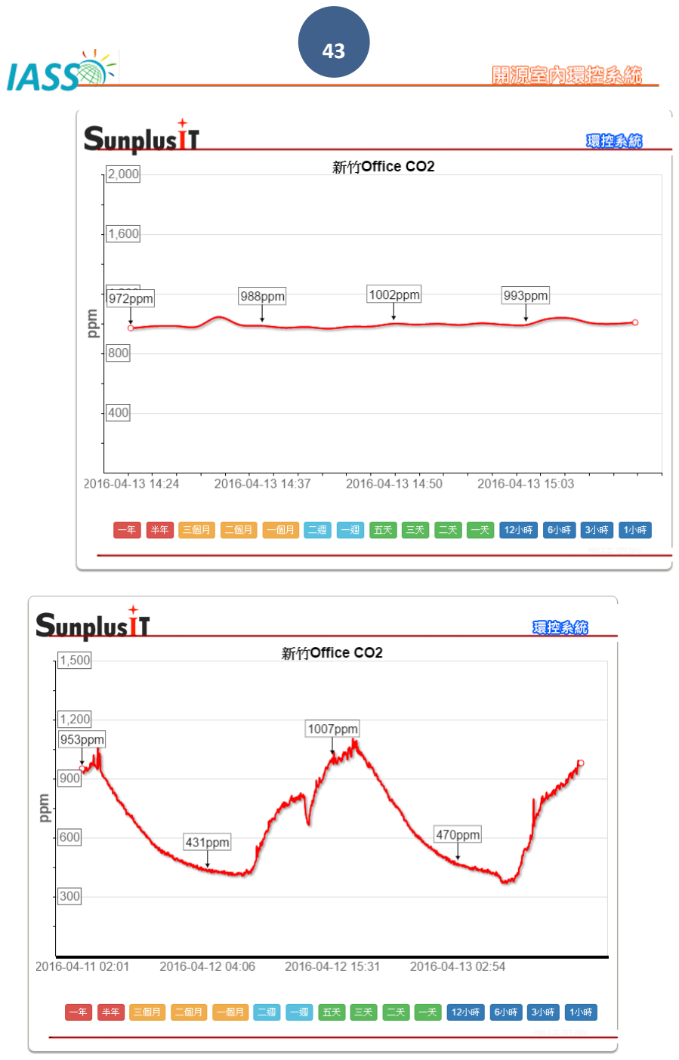
[picture p53: page 43]

44

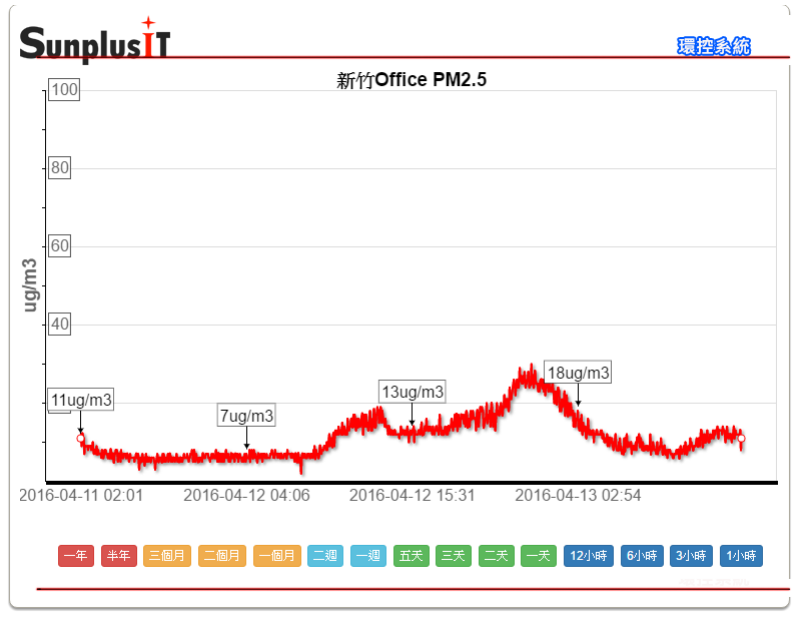
[picture p54: figure]
