LinkItONEDevGroup/LASS/3dp/Scott_Chen/LASS_V3/README.jpg

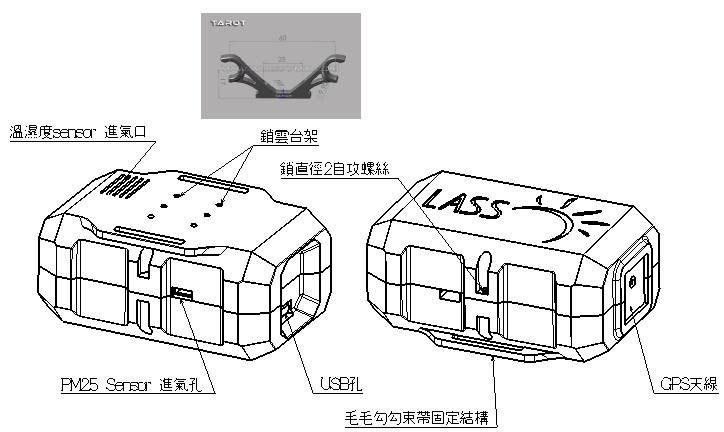
3dp/Scott_Chen/LASS_V3/README.jpg
