LinkItONEDevGroup/LASS/DataPresentation/KmlWithMymapExample1.png

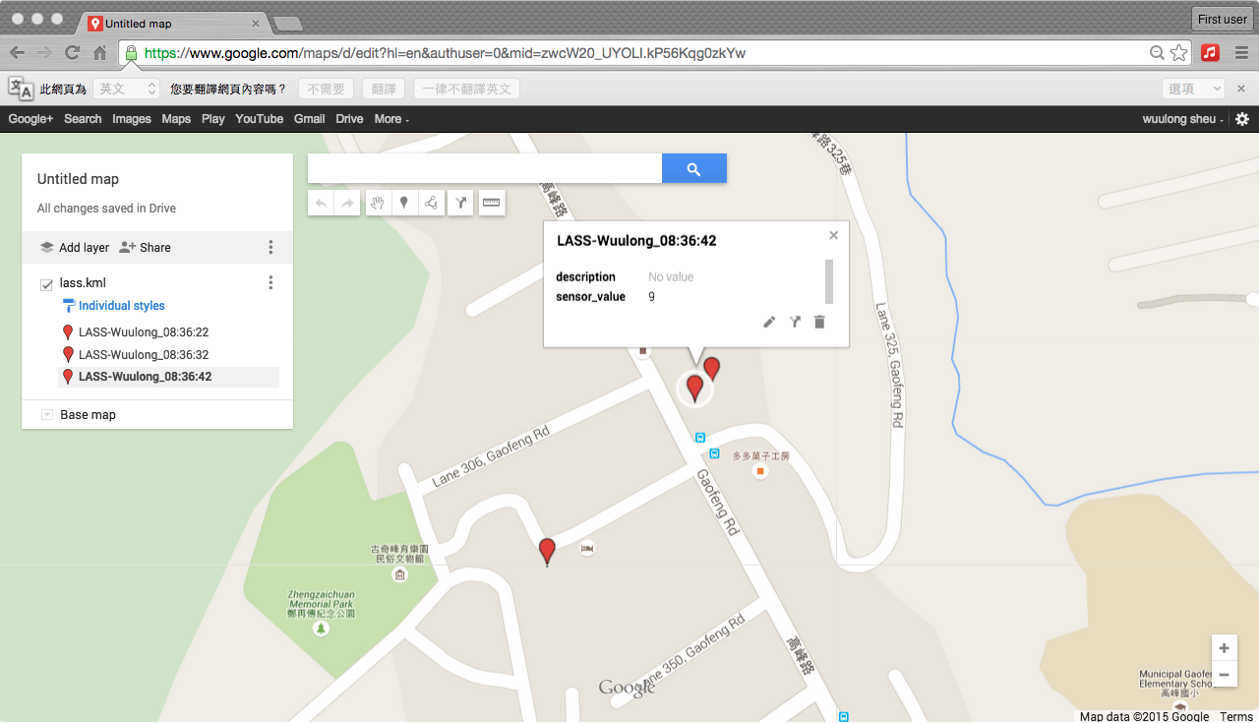
DataPresentation/KmlWithMymapExample1.png
