LinkItONEDevGroup/LASS/DataPresentation/SensorDataExample1.png

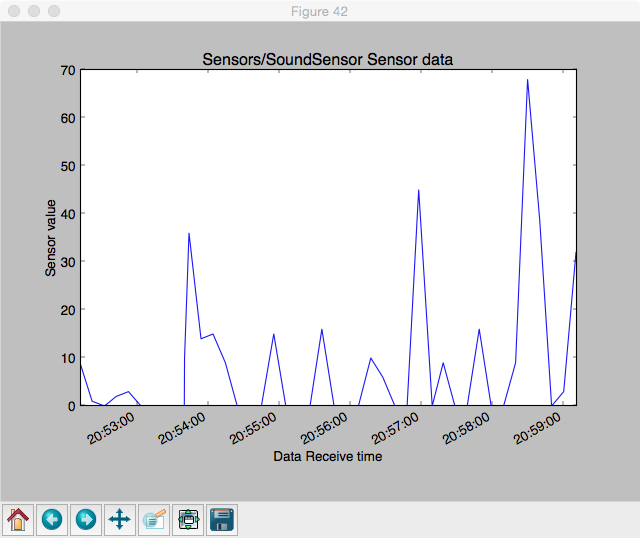
DataPresentation/SensorDataExample1.png
