LinkItONEDevGroup/LASS/Device_LinkItSmart7688Duo/arduino_version/PCB_layout.png

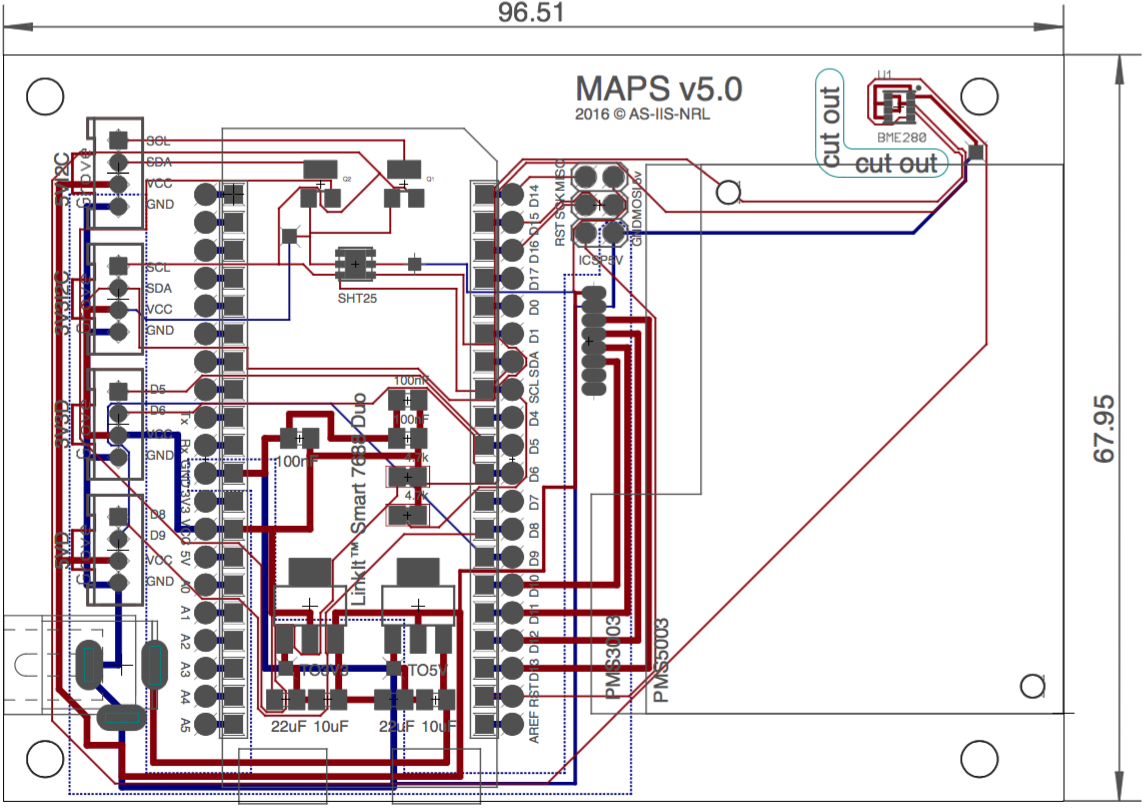
Device_LinkItSmart7688Duo/arduino_version/PCB_layout.png
