LinkItONEDevGroup/LASS/Doc/Blynk_Example1.png

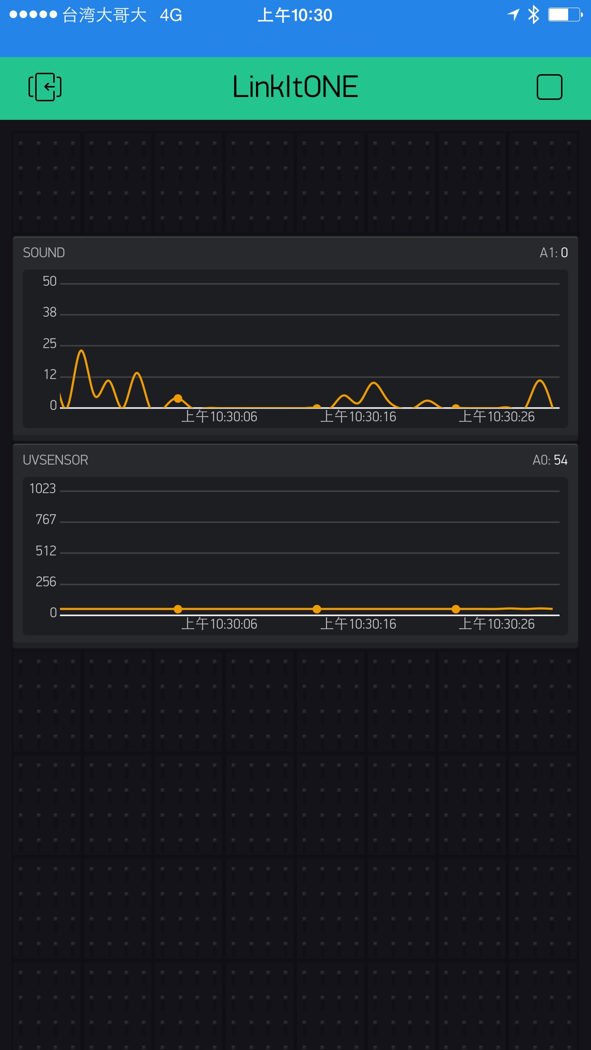
Doc/Blynk_Example1.png
