LinkItONEDevGroup/LASS/Doc/DeviceExample1.jpg

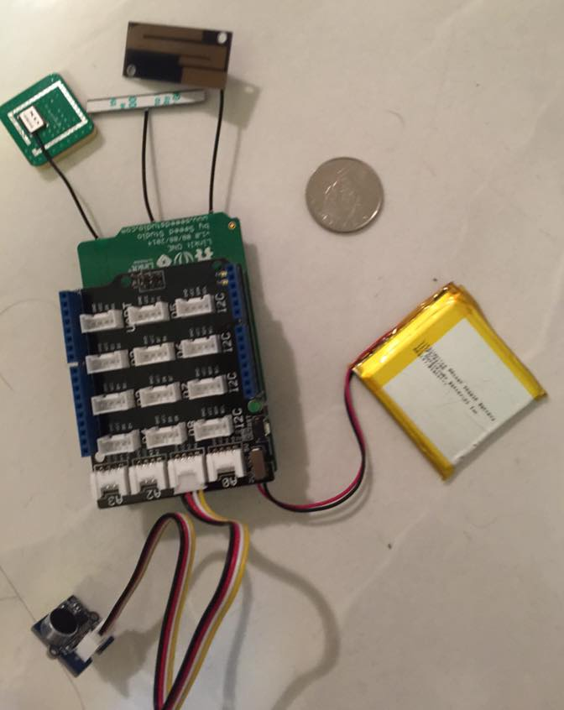
Doc/DeviceExample1.jpg
