LinkItONEDevGroup/LASS/Doc/DeviceExample2.jpg

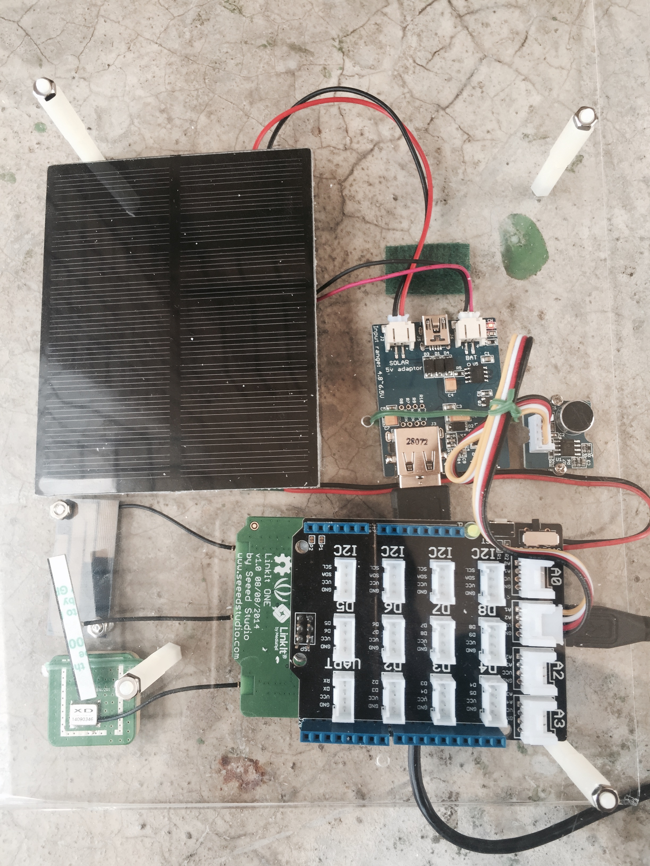
Doc/DeviceExample2.jpg
