LinkItONEDevGroup/LASS/Doc/DustSensor_Example2.png

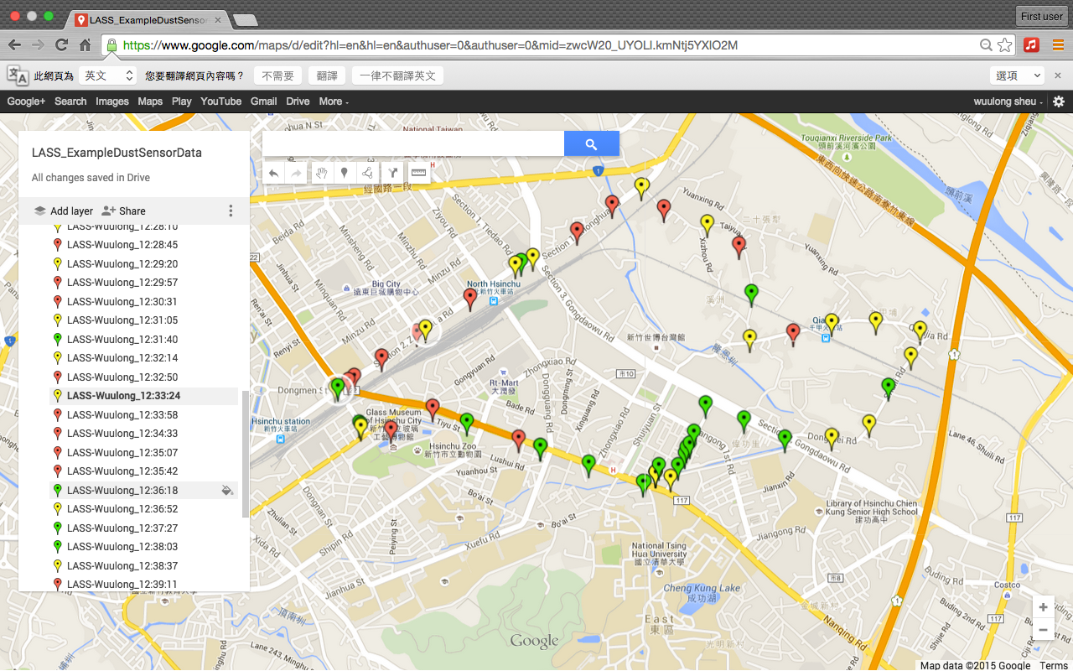
Doc/DustSensor_Example2.png
