LinkItONEDevGroup/LASS/Doc/LASS-AlarmMode.png

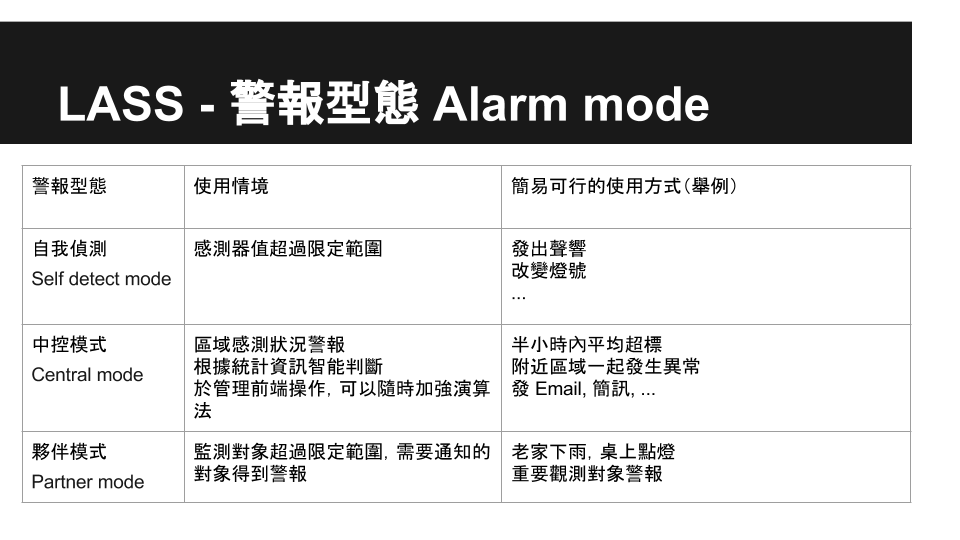
Doc/LASS-AlarmMode.png
