LinkItONEDevGroup/LASS/3dp/Scott_Chen/LASS G3.igs

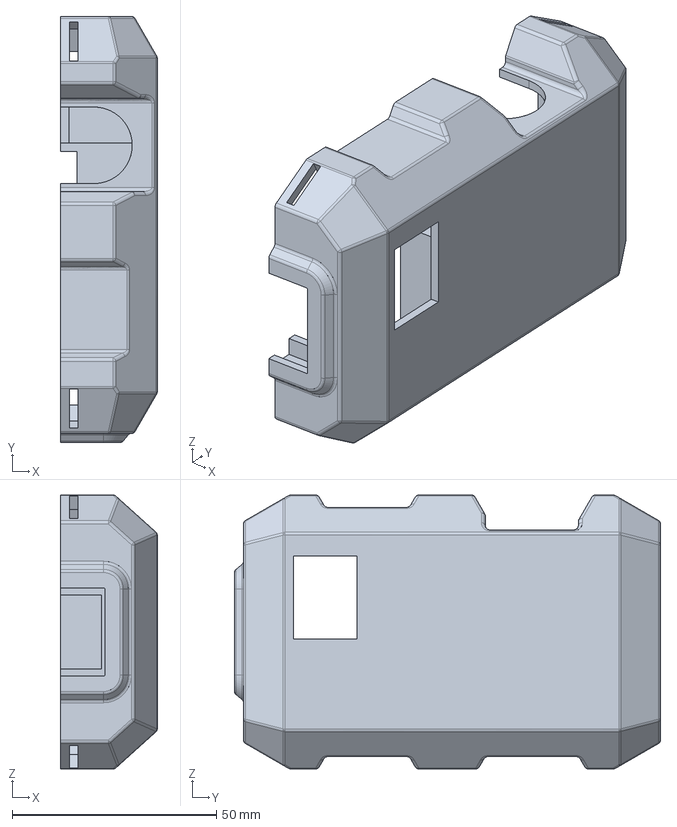
[picture p120: CAD file, 2015-12-14]
3dp/Scott_Chen/LASS G3.igs
23.6 x 104.2 x 67.0 mm
