LinkItONEDevGroup/LASS/3dp/Scott_Chen/LASS4U/LASS4U BOX CAD/Cover.stp

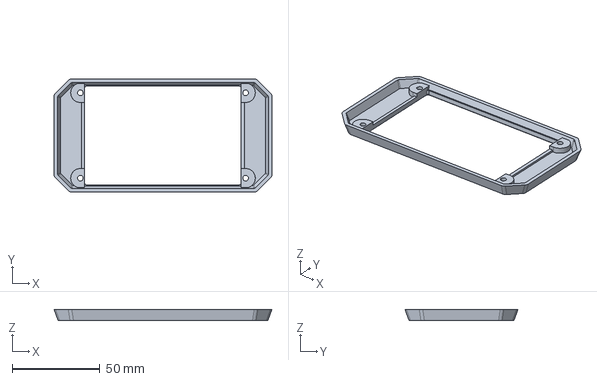
[picture p121: CAD file, 2016-07-07]
3dp/Scott_Chen/LASS4U/LASS4U BOX CAD/Cover.stp
124.1 x 64.4 x 6.50 mm
