LinkItONEDevGroup/LASS/3dp/Scott_Chen/LASS_V3/LASS BOX ver3 over view.stp

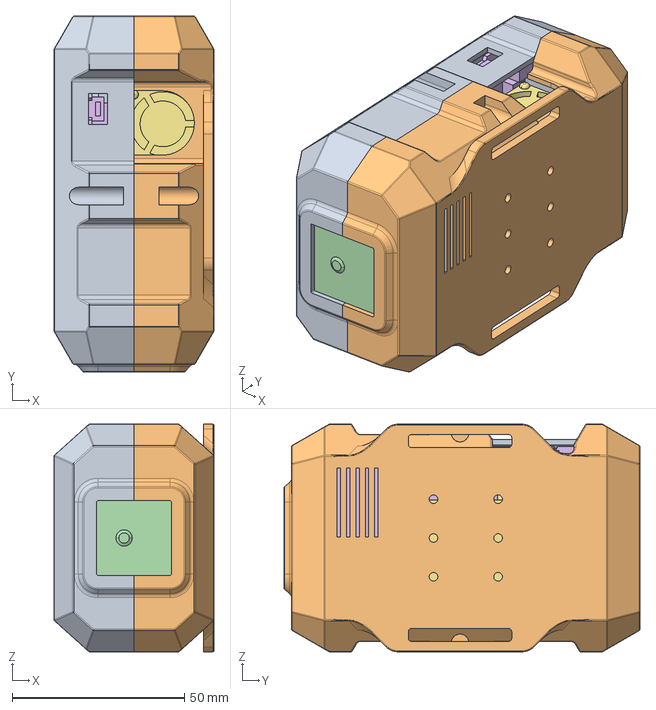
[picture p122: CAD file, 2016-03-10]
3dp/Scott_Chen/LASS_V3/LASS BOX ver3 over view.stp
46.3 x 103.2 x 66.0 mm
