LinkItONEDevGroup/LASS/WaterBox/mechanical/3DP files/SolidWorks file/水質儀器_盒子G386蓋子.SLDPRT

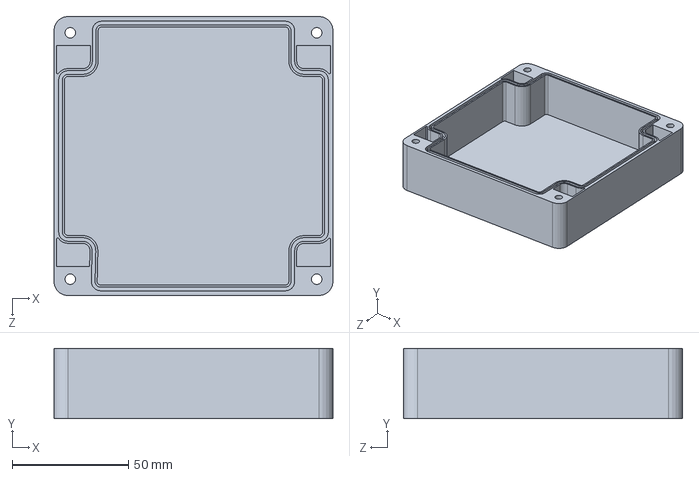
[picture p123: CAD file, 2018-07-22]
WaterBox/mechanical/3DP files/SolidWorks file/水質儀器_盒子G386蓋子.SLDPRT
120.0 x 30.2 x 120.0 mm
