LinkItONEDevGroup/LASS/WaterBox/mechanical/design/PCB板G278C.sldprt

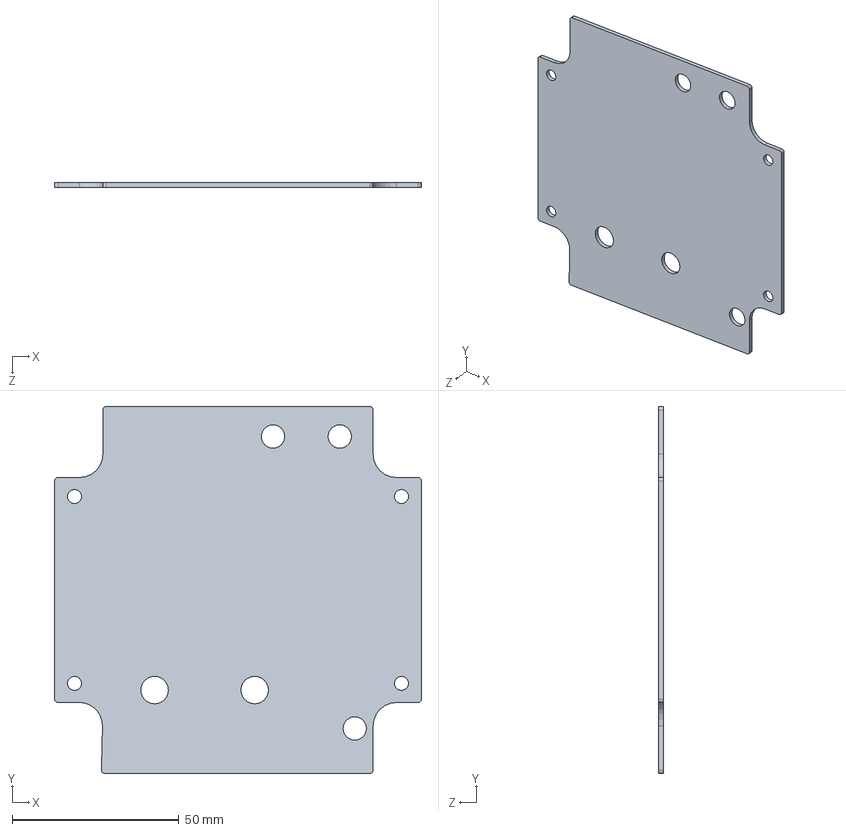
[picture p124: CAD file, 2018-07-22]
WaterBox/mechanical/design/PCB板G278C.sldprt
110.0 x 110.0 x 1.50 mm
