LinkItONEDevGroup/LASS/3dp/RODODO DESIGN/FRAME_V21_MAX_FINAL.stl

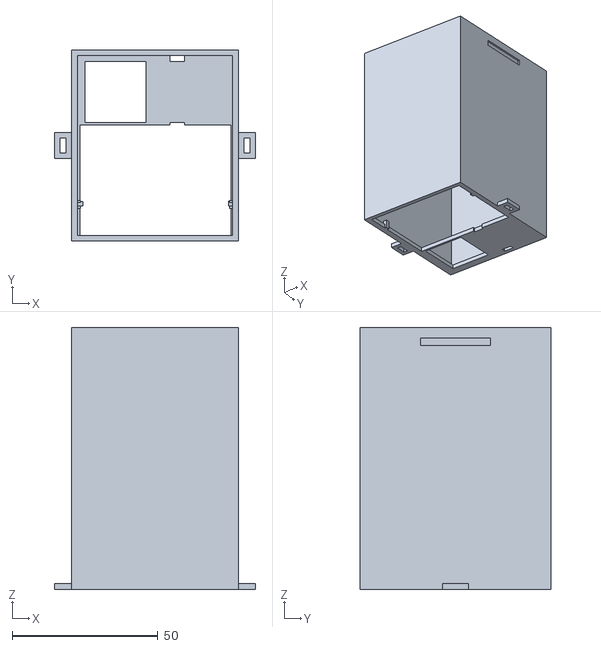
[picture p125: CAD file, 2015-12-01]
3dp/RODODO DESIGN/FRAME_V21_MAX_FINAL.stl
69.2 x 65.7 x 90.0
