LinkItONEDevGroup/LASS/3dp/Scott_Chen/LASS4U/LASS4U BOX CAD/BOX_front.stp

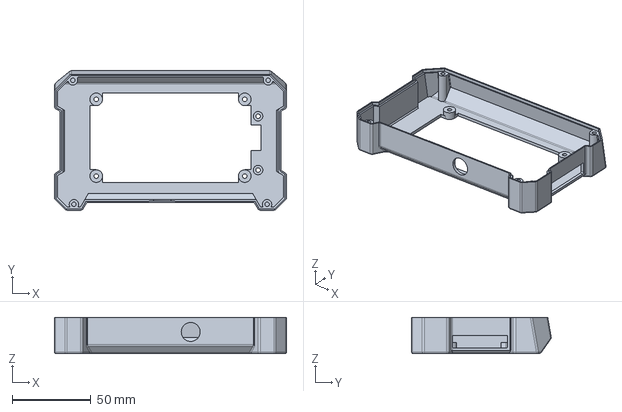
[picture p126: CAD file, 2016-07-07]
3dp/Scott_Chen/LASS4U/LASS4U BOX CAD/BOX_front.stp
147.0 x 88.4 x 23.0 mm
