LinkItONEDevGroup/LASS/WaterBox/mechanical/design/DS3231時間模組.sldprt

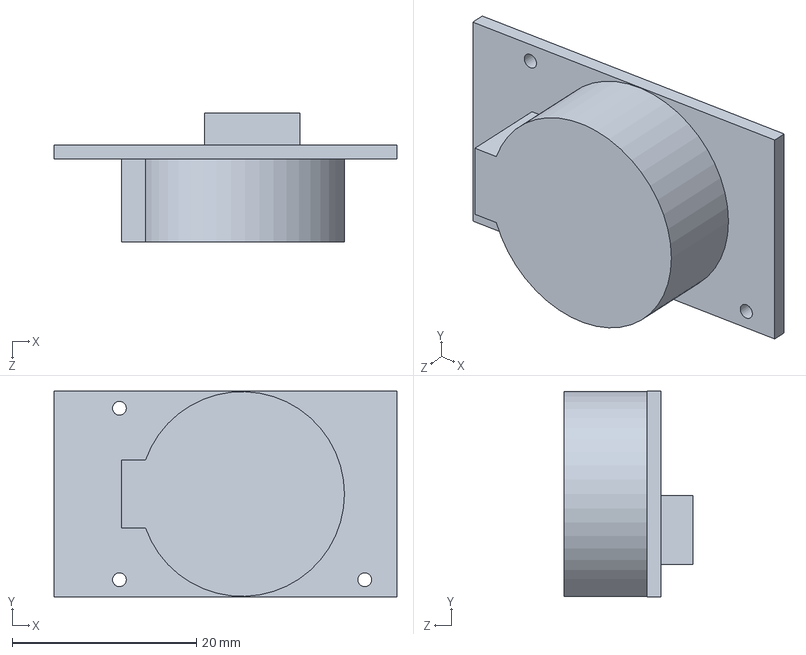
[picture p127: CAD file, 2018-07-22]
WaterBox/mechanical/design/DS3231時間模組.sldprt
37.2 x 22.3 x 14.0 mm
