LinkItONEDevGroup/LASS/3dp/RODODO DESIGN/FRAMELIFT_FINAL.stl

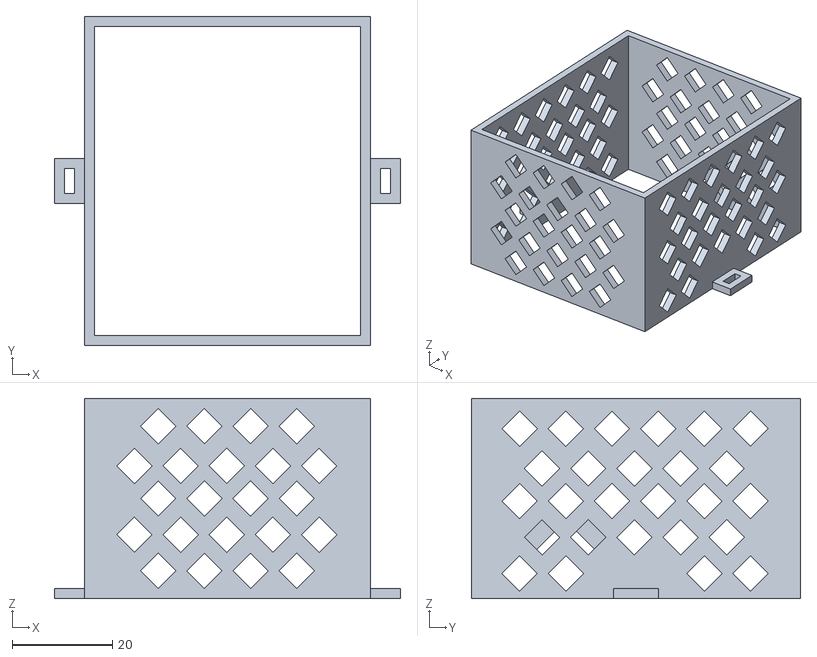
[picture p128: CAD file, 2015-11-28]
3dp/RODODO DESIGN/FRAMELIFT_FINAL.stl
69.2 x 65.7 x 40.0
