LinkItONEDevGroup/LASS/3dp/Scott_Chen/LASS4U/LASS4U BOX CAD/BOX_back.stp

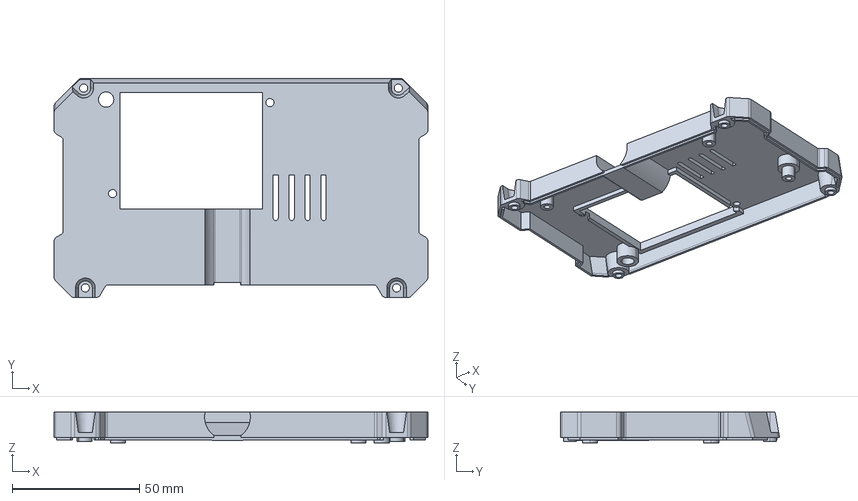
[picture p129: CAD file, 2016-07-07]
3dp/Scott_Chen/LASS4U/LASS4U BOX CAD/BOX_back.stp
147.0 x 86.2 x 12.1 mm
