LinkItONEDevGroup/LASS/WaterBox/mechanical/3DP files/SolidWorks file/溫度模組.sldprt

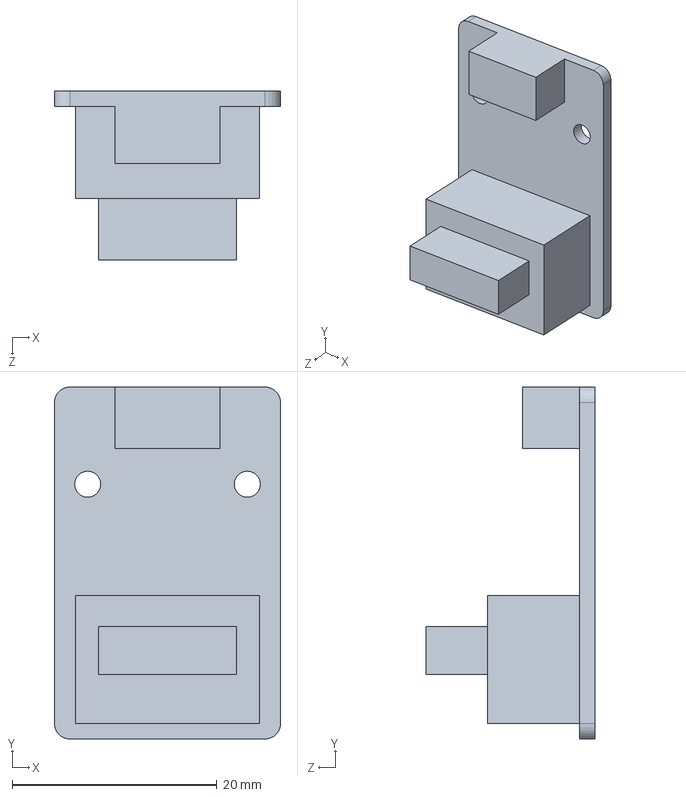
[picture p130: CAD file, 2018-07-22]
WaterBox/mechanical/3DP files/SolidWorks file/溫度模組.sldprt
22.1 x 34.4 x 16.5 mm
