LinkItONEDevGroup/LASS/WaterBox/mechanical/3DP files/SolidWorks file/水質儀器_盒子G386.SLDPRT

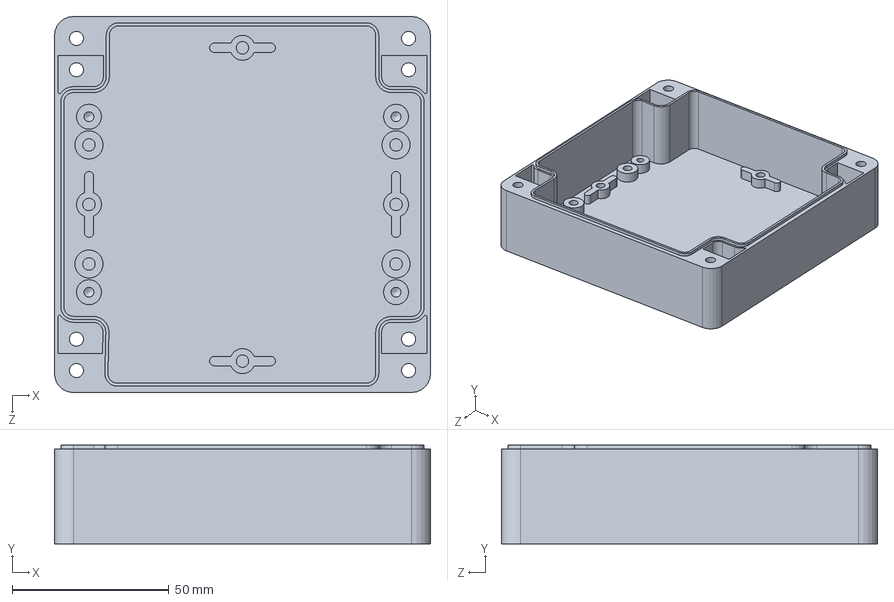
[picture p131: CAD file, 2018-07-22]
WaterBox/mechanical/3DP files/SolidWorks file/水質儀器_盒子G386.SLDPRT
120.0 x 31.5 x 120.0 mm
