LinkItONEDevGroup/LASS/WaterBox/mechanical/3DP files/SolidWorks file/G278C開孔支架.sldprt

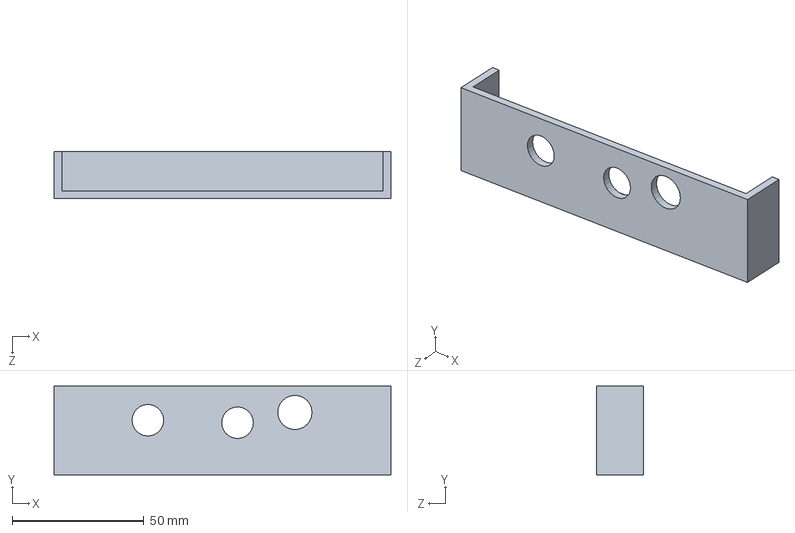
[picture p132: CAD file, 2018-07-22]
WaterBox/mechanical/3DP files/SolidWorks file/G278C開孔支架.sldprt
128.0 x 33.7 x 18.0 mm
