LinkItONEDevGroup/LASS/WaterBox/mechanical/design/底層電池支架G278C.sldprt

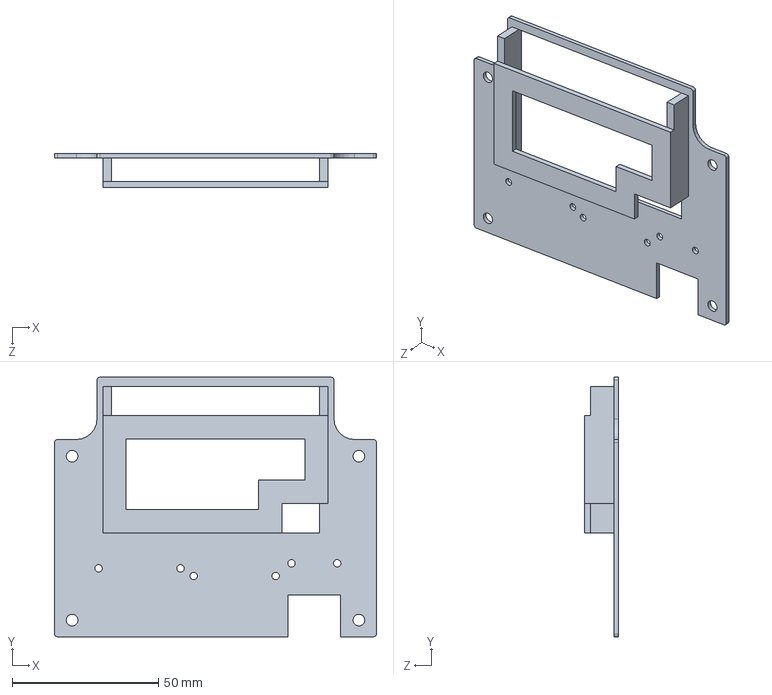
[picture p133: CAD file, 2018-07-22]
WaterBox/mechanical/design/底層電池支架G278C.sldprt
110.0 x 88.7 x 11.5 mm
