LinkItONEDevGroup/LASS/WaterBox/mechanical/design/MTDuino.sldprt

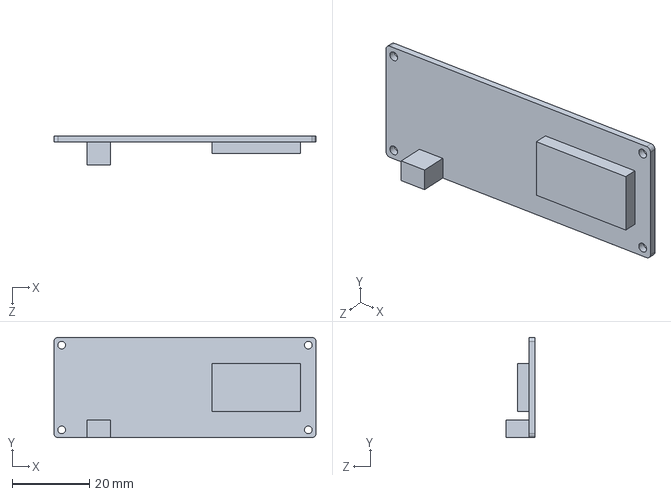
[picture p134: CAD file, 2018-07-22]
WaterBox/mechanical/design/MTDuino.sldprt
68.0 x 26.0 x 7.50 mm
