LinkItONEDevGroup/LASS/WaterBox/mechanical/3DP files/SolidWorks file/EC模組.sldprt

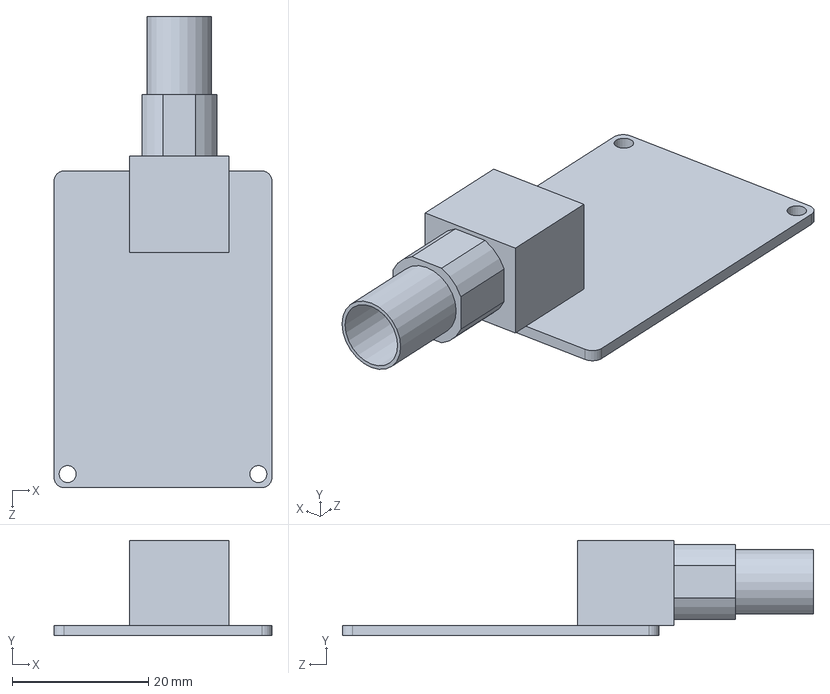
[picture p135: CAD file, 2018-07-22]
WaterBox/mechanical/3DP files/SolidWorks file/EC模組.sldprt
32.0 x 14.0 x 69.2 mm
