LinkItONEDevGroup/LASS/LASS-Simulator/doc/LASS Simulator.pdf

# LASS Simulator

開發步驟
確認執行環境
架構設計
系統基礎帶起
CLI start
Log start
CFG start
simulation installation check
unit test start
start car, Deposition, status with simulation plot total value
export ESRI for single and animation
支援初始化地理位置設定
limit wind effect

需求

希望能有效模擬 PM2.5 感測現象進而提供一些實驗設計參考

規格

模擬功能
能模擬因人口車輛的影響
能模擬特定燃燒工廠排放的影響
能模擬境內與境外之間的移動特性比方說境外污染影響
能區分高空與低空污染
能模擬下雨沈積風颱風的效應
能模擬特定氣候效應
能模擬特定區域現象
模擬區域特性如地理特性能有標準介面以提供匯入定義
模擬結果能與目前實際感測值做比較
能做小時天週月年的模擬

系統功能
開源分享
主設計使用 Python
使用 SimPy , NumPy
使用者參數集中管理與設定
核心使用 Command line interface
方便客製化設計
支援結果繪出 ESRI ASCII Raster format, 能支援動態模擬
工廠資訊匯入

設計

基本
時間單位分鐘
空間單位1m 平方1m 立方
Cfg : 設定參數包含各個 Producer 的常態特性動態特性參數 有邊界

Producer
Village : 一般性的內含人車以及基本產生量
Population : 人口
Car : 車輛
Factory :
Combustion : 特定燃燒

Consumer
Climate : 下雨颱風等
Deposition : 沈積
Effect
Wind :
Diffusion :
Boundry
邊界只有平均值沒有累積量

Status
Map : 整張地圖
Position : 固定長寬的空間用 X@Y 來 index pm_total : pm 總量
pm_value : pm 量測值 ug/m3
Area : 一堆 Position 的組合

設定
地理
以經緯度範圍設定模擬區域
精細度可選
100m, 1km, 10km

基本演算法

持續 monitor status
Producers 給予特定的產生條件持續產生
Consumer 持續減少數值
Apply effects

total value
固定空間大小來當除數
配上高度比例分成生活段可量測與高空段未量測

跨邊界效應
邊界以 value 標示total 無限
污染離開邊界會更新邊界 value 值
污染由邊界傳入需計算 value * 時間為傳入量 邊界值可以依模擬條件隨時更新或由模擬條件漸進更新

## Files/Directories Definition

doc
README.txt : release note
Codes : codes
Include :
sim.ini
Output
ESRI export naming rule:
output/name_timestamp.asc (ex: abc_20160708210000.asc) output/name.xml
sim.log : system log
Lib : the code that may easy to be reused
test:
sim.py : startup program

## 帶起步驟設計

Basic fundation, classes/cfg/reporting
車輛與沈積效應的平衡
Wind effect + boundry handler
大地圖 grouping 走向全台灣模擬
Climate effect
Real data input, real data comparsion

## Versions

V0.0.1
Basic application fundation, CFG, logging, CLI, unit test, simulation Quick support Deposition, Car, Population
V0.1
Export ESRI
Some setting from file
Quick wind effect

## Installation

We use python 3
pip3 install simpy
pip3 install configobj
pip3 install matplotlib
pip3 install numpy

執行
python3 sim.py

## Study

Plot Data Points on a Map

## Current Progress

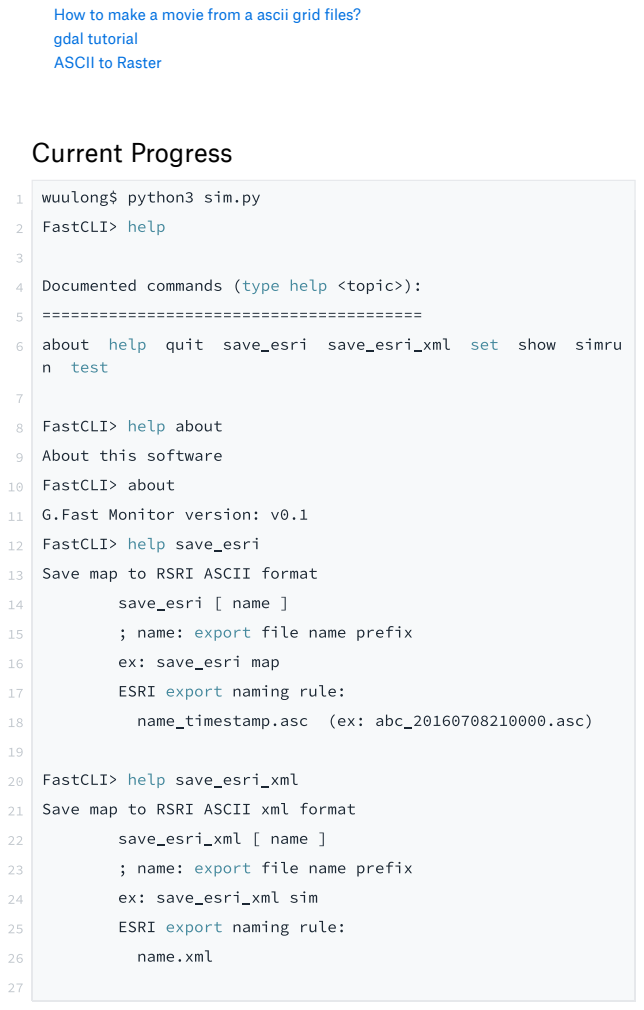
[picture p145: page 5]

How to make a movie from a ascii grid files?
gdal tutorial
ASCII to Raster

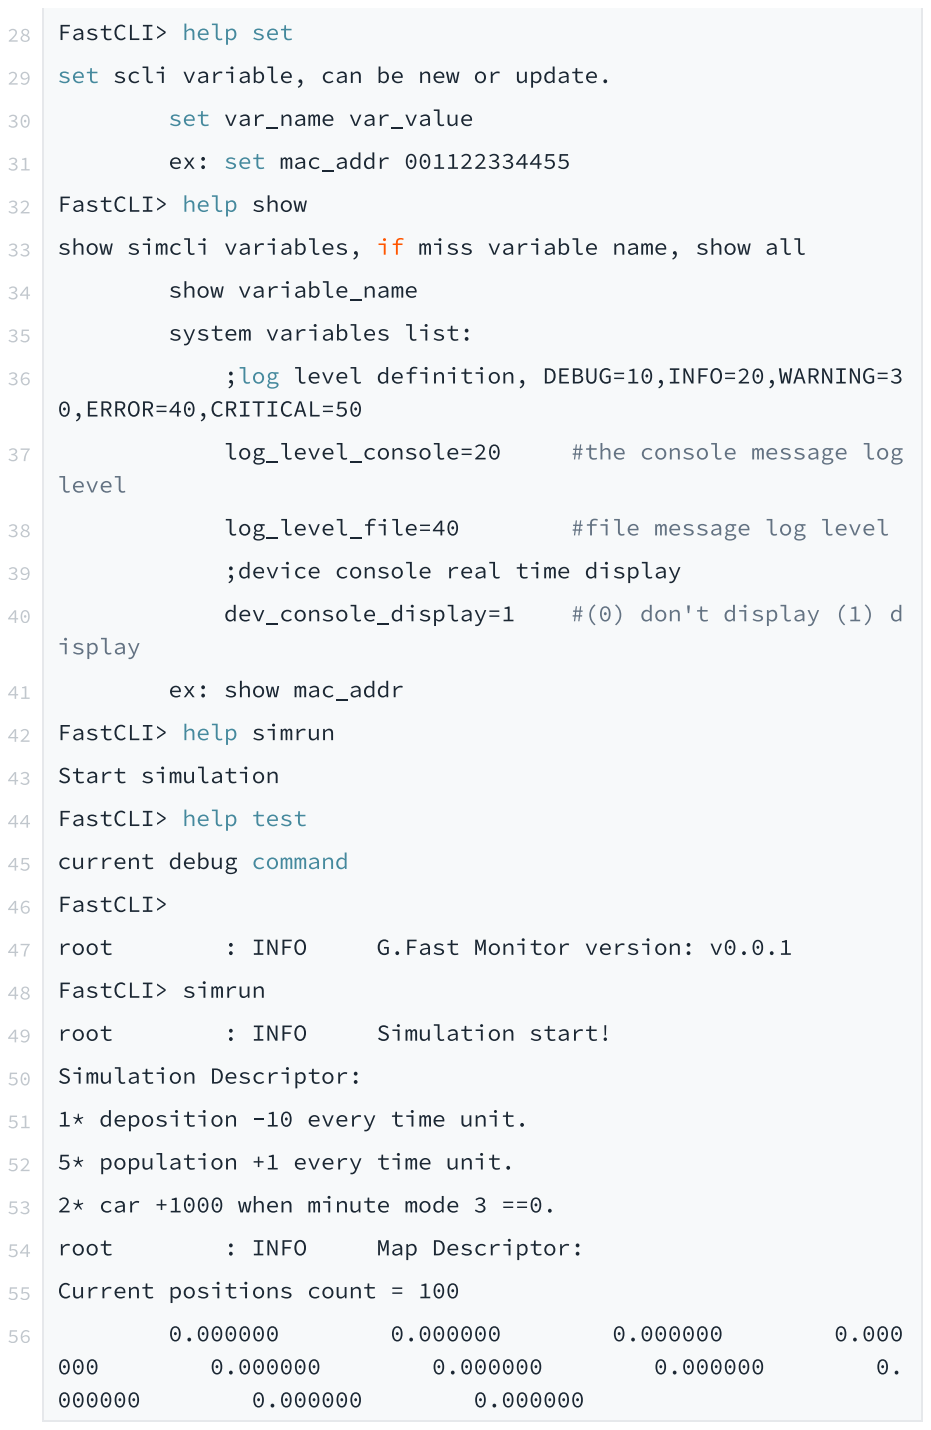
[picture p146: page 6]

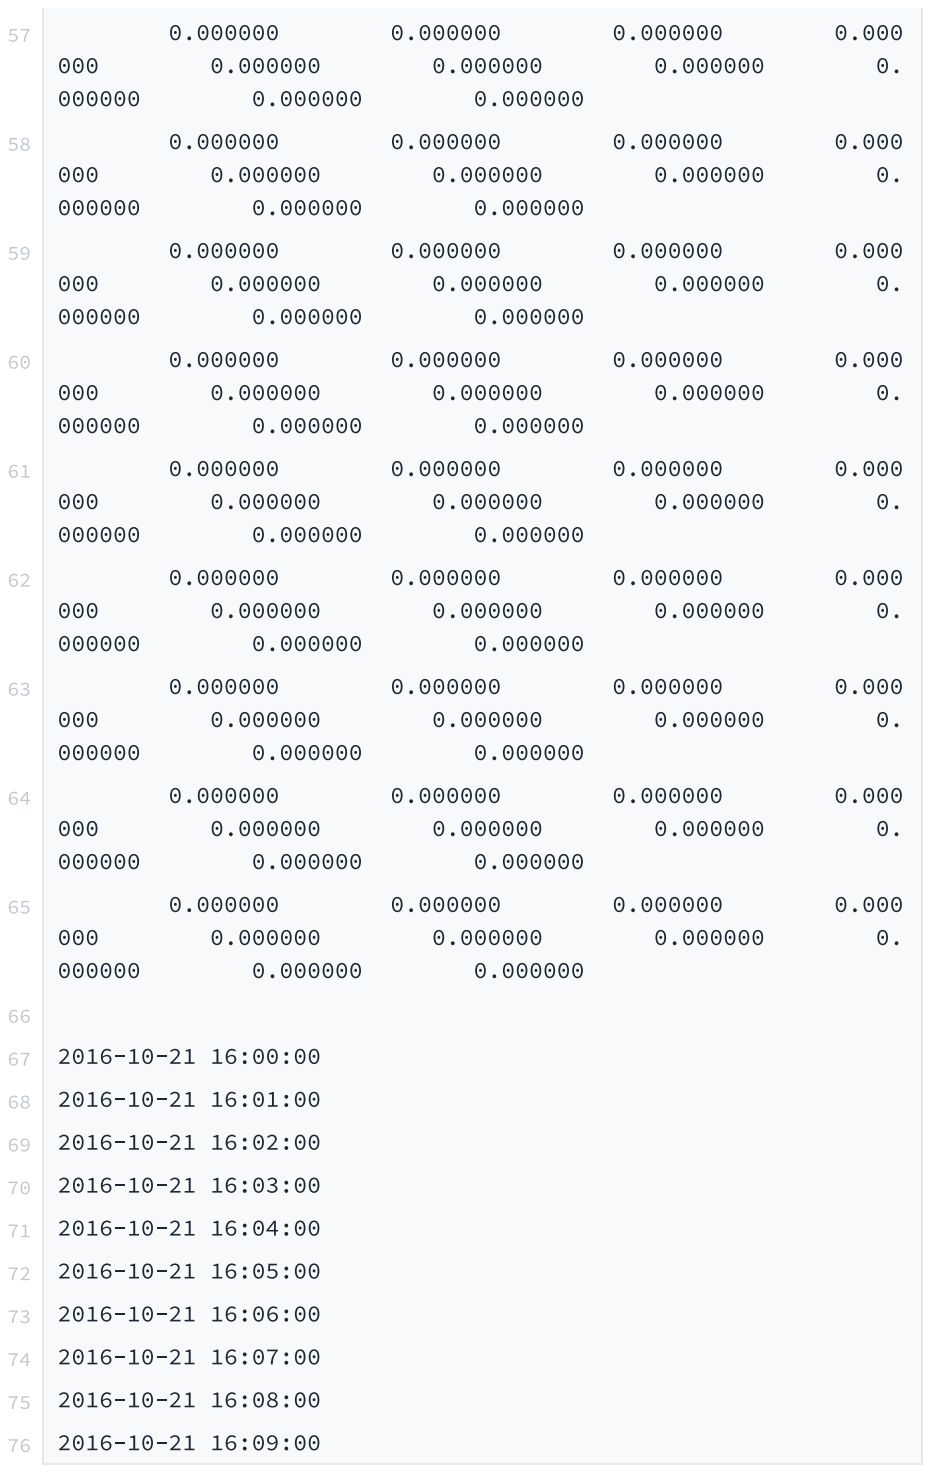
[picture p147: page 7]

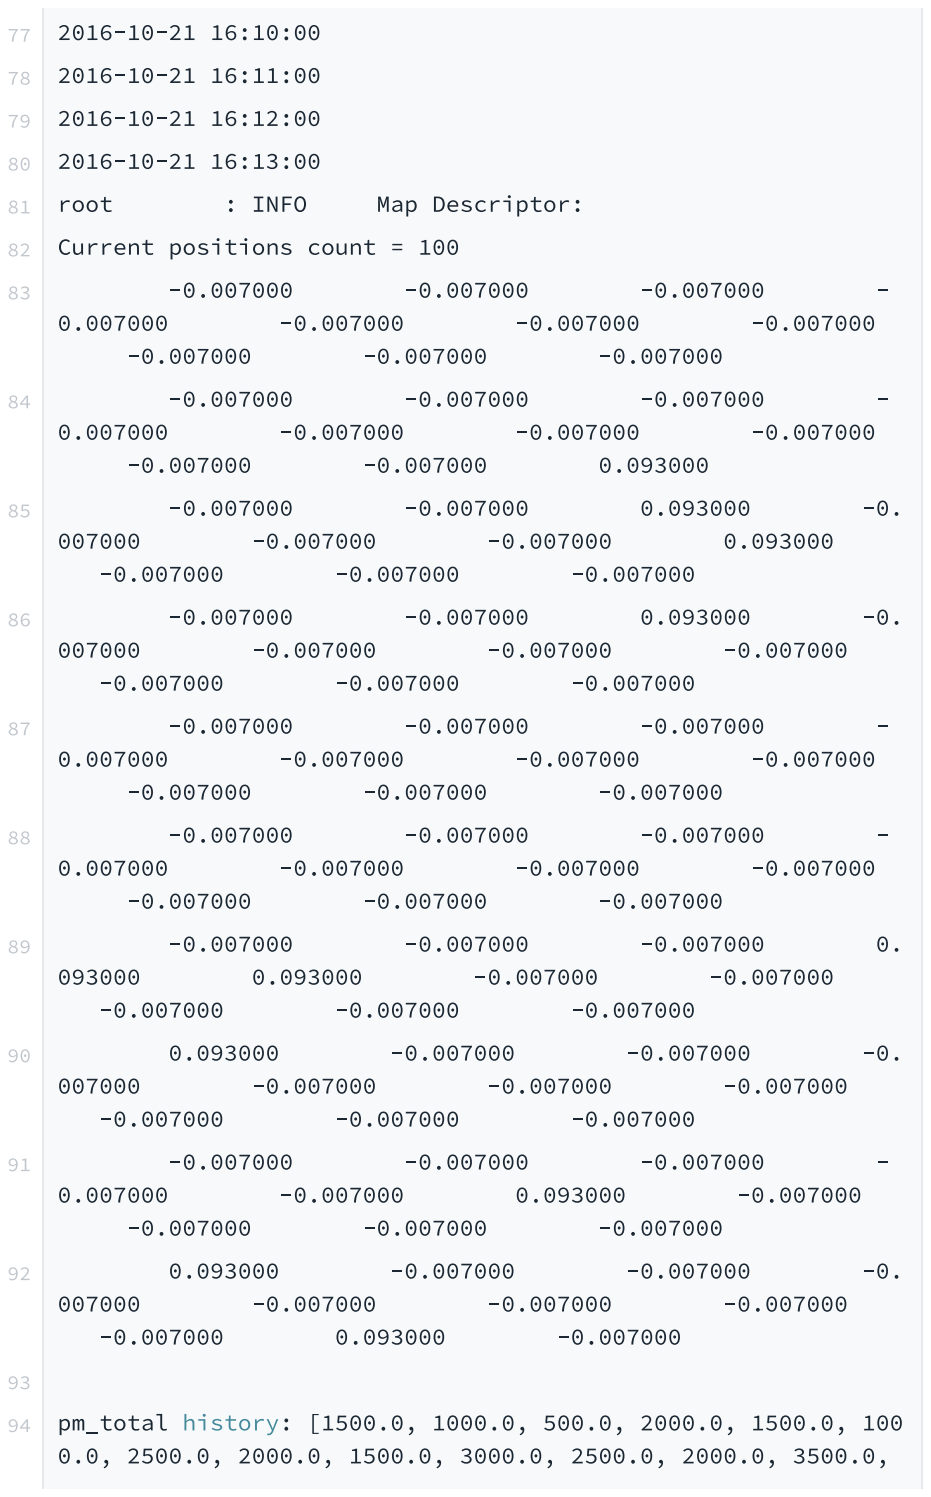
[picture p148: page 8]

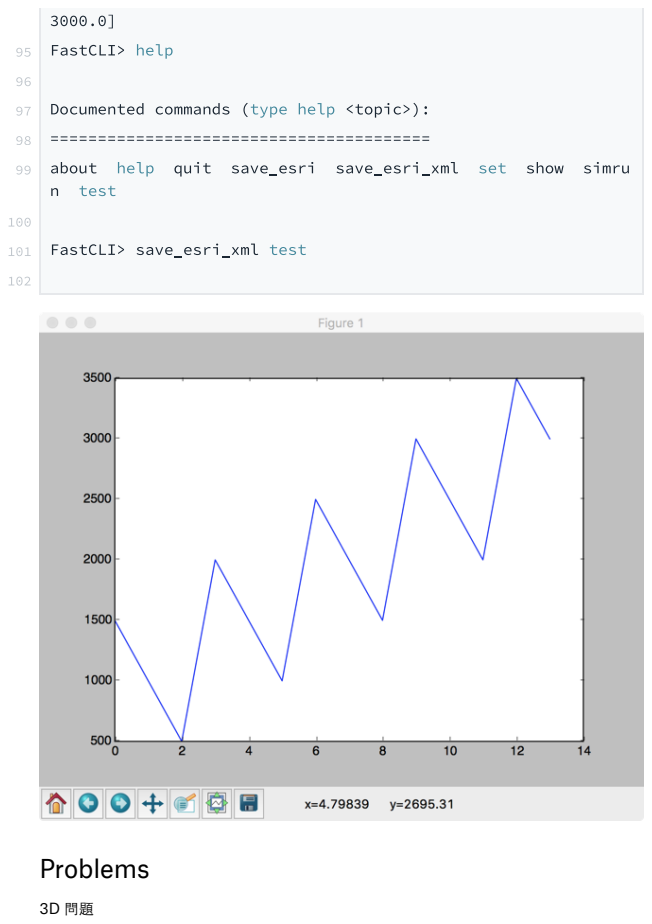
[picture p149: page 9]
Problems
