LinkItONEDevGroup/LASS/3dp/Scott_Chen/LASS README.pdf

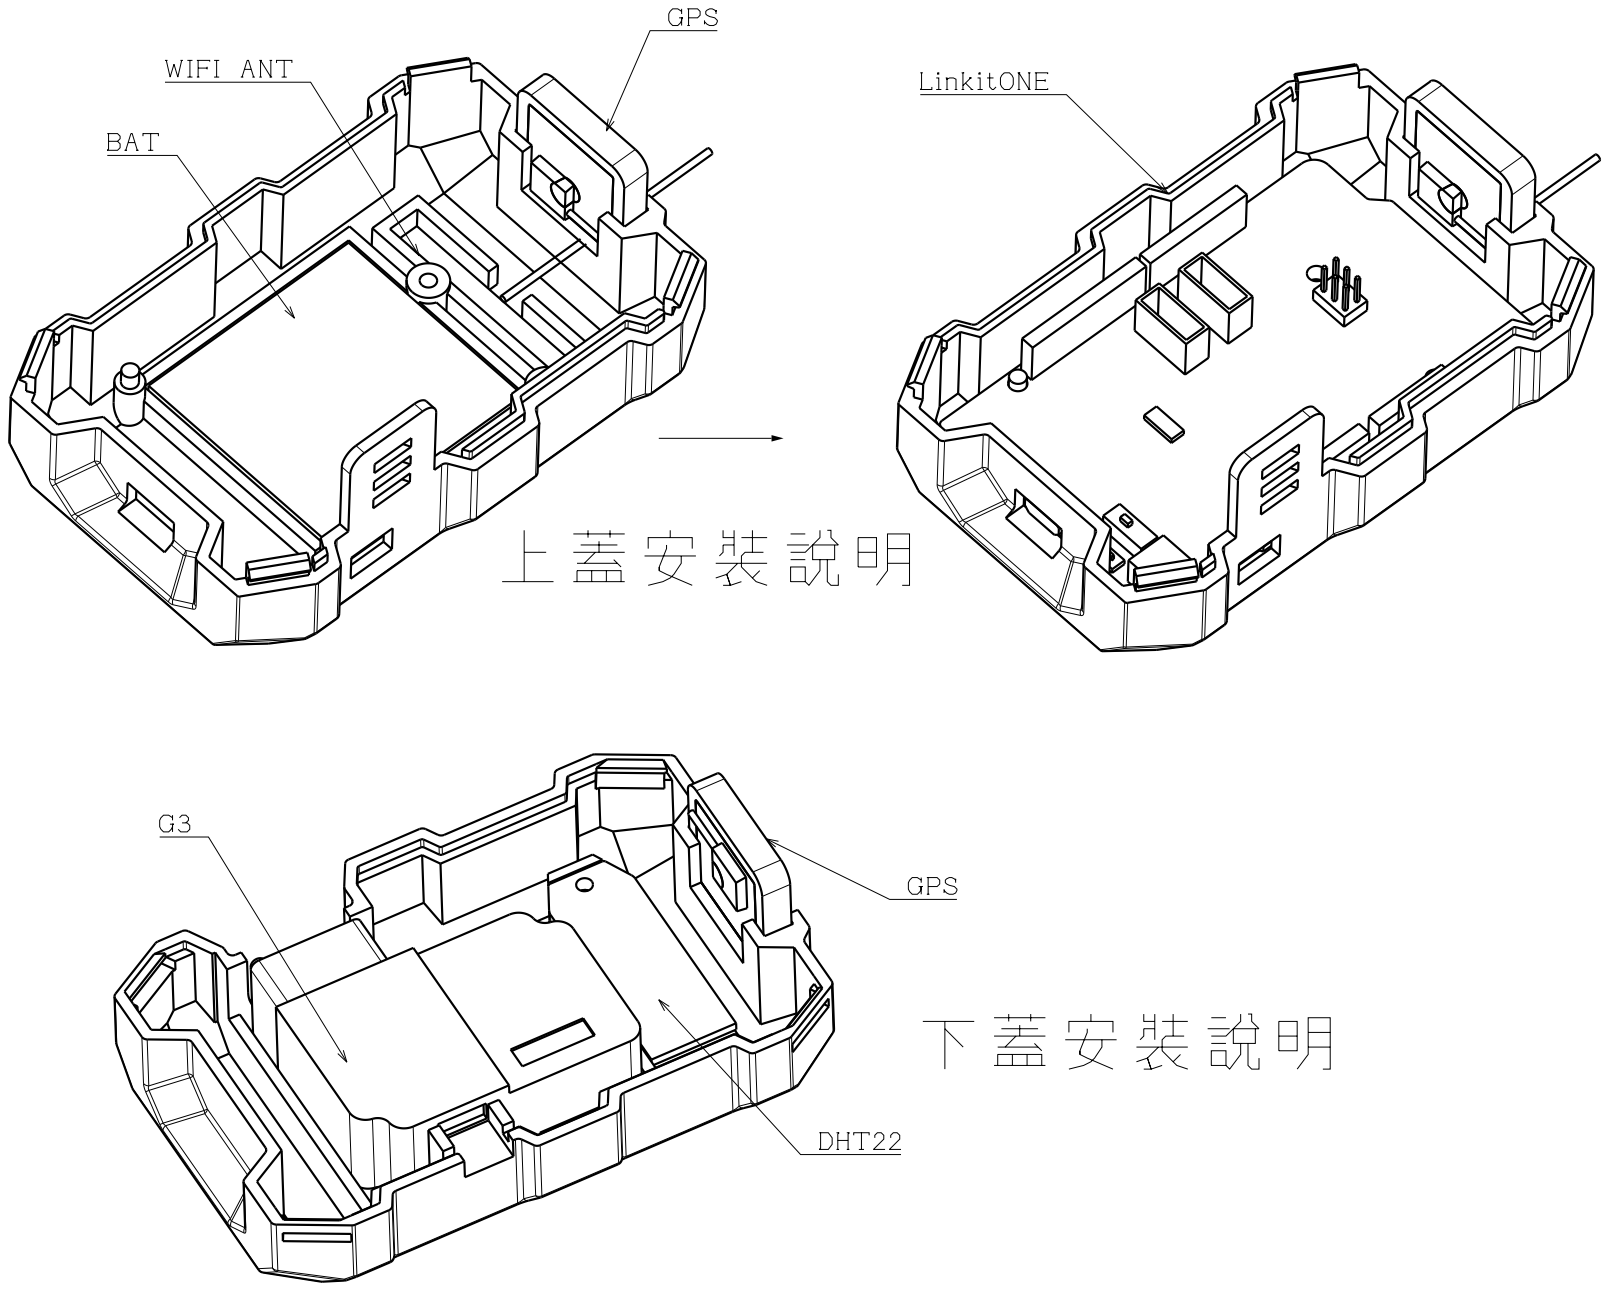
[picture p150: page 1]
