LinkItONEDevGroup/LASS/IASS/IASS_BASIC/Sensors_support/MQ2/MQ2.ino

#define gasMQ2Pin A2


class deviceMQ2 {    
  public:
    deviceMQ2() {
      
    }

    float readValue() {
      return analogRead(gasMQ2Pin);
    }
};

deviceMQ2 sensorMQ2;

void setup() {
  Serial.begin(9600);
  Serial.println("MQ2 test!");

}

void loop() {
  Serial.println(sensorMQ2.readValue());
  delay(2000);    
}  
