LinkItONEDevGroup/LASS/IASS/IASS_BASIC/Sensors_support/FC-37/FC-37.ino

#define waterPin A3

class deviceFC37 {    
  public:
    deviceFC37() {
    }

    float readValue() {
       int sensorRead = analogRead(waterPin);
       //return (sensorRead*100)/1023;
       int ratio = 100-(sensorRead/10);
       if(ratio<0) {
          return 0;
       }else if(ratio>100) {
          return 100;
       }else{
          return ratio;
       }
    }
};

deviceFC37 sensorFC37;

void setup() {
  Serial.begin(9600);
  Serial.println("FC-37 test!");

}

void loop() {
  Serial.print(sensorFC37.readValue());  //回傳值為漏水的機率, 單位%
  Serial.println('%');
  delay(2000);
    
}  
