LinkItONEDevGroup/LASS/Companion-module/Arduino Side/LASSCompanion/images.c

#include <avr/pgmspace.h>


const static unsigned char PROGMEM cbartop[] = {
0x00, 0x00, 0x00, 0x00, 0x00, 0x00, 0x00, 0x00, 0x00, 0x00, 0x00, 0x00, 0x00, 0x00, 0x00, 0x00,
0x00, 0x00, 0x00, 0x00, 0x00, 0x00, 0x00, 0x00, 0x00, 0x00, 0x00, 0x00, 0x00, 0x00, 0x00, 0x00,
0x00, 0x00, 0x00, 0x00, 0x0F, 0xE4, 0x10, 0x07, 0x01, 0x8C, 0x01, 0x49, 0xE2, 0x2F, 0xEF, 0x10,
0x1C, 0x04, 0x1A, 0x68, 0xEA, 0xA4, 0xFE, 0x11, 0x00, 0x90, 0x7F, 0xE5, 0x2A, 0x28, 0x29, 0x1C,
0x08, 0x04, 0x26, 0x98, 0x4F, 0xE4, 0x48, 0x11, 0x07, 0xFE, 0x41, 0x01, 0x2A, 0x5A, 0xA9, 0x24,
0x08, 0x0A, 0x22, 0x88, 0x40, 0x0E, 0xFE, 0x20, 0x81, 0xB0, 0x7F, 0x49, 0xEA, 0xEF, 0xEF, 0x68,
0x08, 0x0A, 0x10, 0x40, 0xEF, 0xE4, 0x00, 0x40, 0x42, 0x08, 0x5D, 0x85, 0x2A, 0x29, 0x22, 0x90,
0x08, 0x0A, 0x08, 0x20, 0x44, 0x44, 0xFC, 0x88, 0x24, 0x04, 0x54, 0xA1, 0xEA, 0x5F, 0xEA, 0x28,
0x08, 0x0E, 0x04, 0x10, 0x47, 0xC4, 0x84, 0x08, 0x0B, 0xFA, 0x5D, 0x65, 0x2A, 0xFA, 0x2B, 0xC6,
0x08, 0x91, 0x22, 0x88, 0x72, 0xA6, 0xFC, 0x11, 0x02, 0xA8, 0x80, 0x05, 0xEA, 0x2A, 0x2A, 0x7C,
0x09, 0x11, 0x32, 0xC8, 0xCC, 0xCC, 0xFC, 0x10, 0x82, 0xA8, 0x54, 0x4C, 0x02, 0xAB, 0xAA, 0x44,
0x1F, 0x3B, 0xAC, 0xB0, 0x17, 0x40, 0x52, 0x3F, 0xC2, 0xA8, 0x52, 0xA4, 0xA2, 0xA8, 0x2B, 0x44,
0x00, 0x00, 0x00, 0x00, 0x0C, 0x23, 0x9E, 0x60, 0x4F, 0xFE, 0x9F, 0x85, 0x2E, 0x28, 0xEC, 0x7C,
0x00, 0x00, 0x00, 0x00, 0x00, 0x00, 0x00, 0x00, 0x00, 0x00, 0x00, 0x00, 0x00, 0x00, 0x00, 0x00,
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
0x07, 0x0F, 0x80, 0x7D, 0x80, 0x33, 0x90, 0x1E, 0x70, 0x00, 0x00, 0x00, 0x00, 0x00, 0x00, 0x00,
0x07, 0x00, 0x00, 0x7D, 0x97, 0x01, 0xA0, 0x10, 0x49, 0x80, 0x00, 0x00, 0x00, 0x00, 0x00, 0x00,
0x07, 0x00, 0x01, 0xF8, 0x1F, 0x01, 0xE0, 0x10, 0x48, 0x00, 0x00, 0x00, 0x00, 0x00, 0x00, 0x00,
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
};
