LinkItONEDevGroup/LASS/Device_LinkItSmart7688Duo/python_version/Example/OTA_RODODO/MakerPRO2.ino

/*
  ReadAnalogVoltage
  Reads an analog input on pin 0, converts it to voltage, and prints the result to the serial monitor.
  Attach the center pin of a potentiometer to pin A0, and the outside pins to +5V and ground.

 This example code is in the public domain.
 */

// the setup routine runs once when you press reset:
void setup() {
  // initialize serial communication at 9600 bits per second:
  Serial.begin(9600);
}

// the loop routine runs over and over again forever:
void loop() {
  Serial.println("This is OLD version that I have only 9 properties.");
  delay(1000);
}
